nmarcovecchio/cof/docs/voice/operators/README.md

# Operadores

Una carpeta por red. Lo que acá se afirma salió de pruebas en lab, no de
la ficha comercial del operador.

| Carpeta | Red | MCC/MNC | Lab |
|---|---|---|---|
| [claro-ar.md](claro-ar.md) | Claro Argentina | `722310` | `cof-test`, A7672SA-FASE |

Cuando entre otra SIM, copiá el mismo esquema de eventos (`ATD`, ringing,
reject, no-answer, answer, hangup) y no reutilices las conclusiones de Claro.
