nmarcovecchio/cof/hardware/kicad/01-alimentacion.kicad_sch

## KiCad design hardware/kicad/01-alimentacion.kicad_sch (2026-10-06)

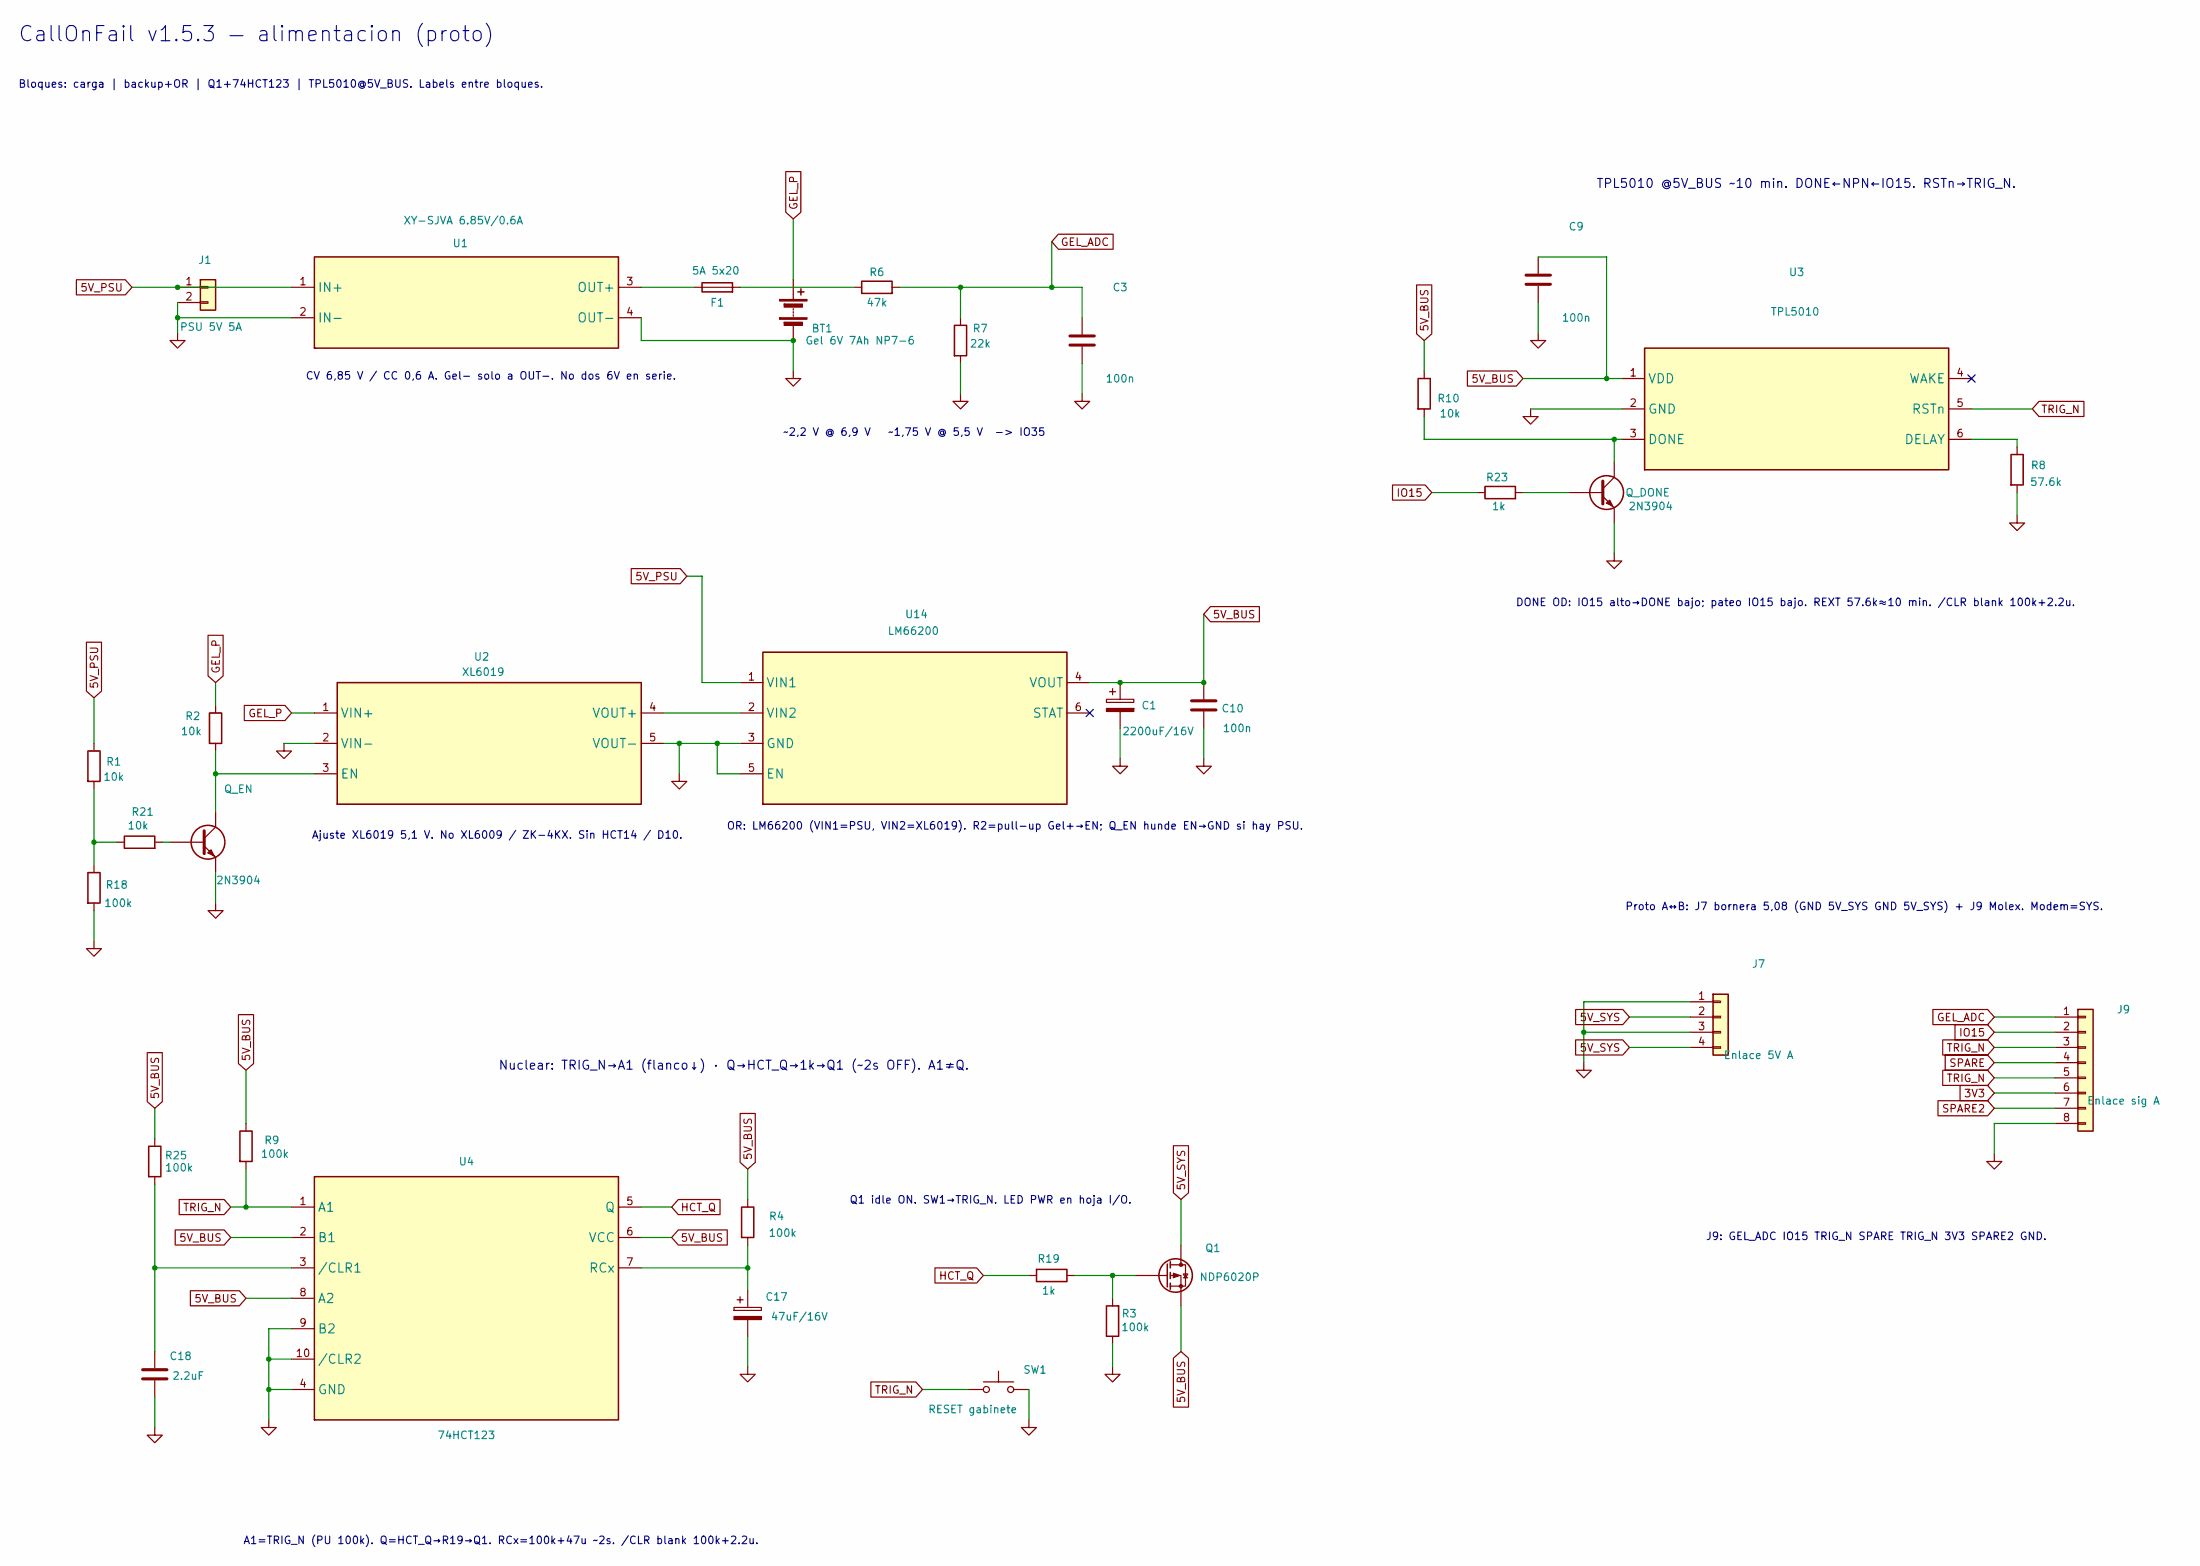
[picture p5: schematic 01-alimentacion.kicad_sch]

Parts:
BT1: Gel 6V 7Ah NP7-6
C1: 2200uF/16V
C3, C9, C10: 100n
C17: 47uF/16V
C18: 2.2uF
F1: 5A 5x20
J1: PSU 5V 5A
J7: Enlace 5V A
J9: Enlace sig A
Q1: NDP6020P
Q_DONE: 2N3904
Q_EN: 2N3904
R1, R2, R10, R21: 10k
R3, R4, R9, R18, R25: 100k
R6: 47k
R7: 22k
R8: 57.6k
R19, R23: 1k
SW1: RESET gabinete
U1: XY-SJVA 6.85V/0.6A
U2: XL6019
U3: TPL5010
U4: 74HCT123
U14: LM66200

Connections:
3V3: J9.6
5V_BUS: C1.1, C9.1, C10.1, Q1.S, R4.1, R9.1, R10.1, R25.1, U3.1 (VDD), U4.2 (B1), U4.6 (VCC), U4.8 (A2), U14.4 (VOUT)
5V_PSU: J1.1, R1.1, U1.1 (IN+), U14.1 (VIN1)
5V_SYS: J7.2, J7.4, Q1.D
GEL_ADC: C3.1, J9.1, R6.2, R7.1
GEL_P: BT1.1 (+), R2.1, U2.1 (VIN+)
GND: BT1.2 (-), C1.2, C3.2, C9.2, C10.2, C17.2, C18.2, J1.2, J7.1, J7.3, J9.8, Q_DONE.E, Q_EN.E, R3.1, R7.2, R8.2, R18.2, SW1.2, U1.2 (IN-), U1.4 (OUT-), U2.2 (VIN-), U2.5 (VOUT-), U3.2 (GND), U4.4 (GND), U4.9 (B2), U4.10 (/CLR2), U14.3 (GND), U14.5 (EN)
HCT_Q: R19.2, U4.5 (Q)
IO15: J9.2, R23.1
unnamed: C17.1, R4.2, U4.7 (RCx)
unnamed: C18.1, R25.2, U4.3 (/CLR1)
unnamed: F1.1, U1.3 (OUT+)
unnamed: F1.2, R6.1
unnamed: Q1.G, R3.2, R19.1
unnamed: Q_DONE.B, R23.2
unnamed: Q_DONE.C, R10.2, U3.3 (DONE)
unnamed: Q_EN.B, R21.2
unnamed: Q_EN.C, R2.2, U2.3 (EN)
unnamed: R1.2, R18.1, R21.1
unnamed: R8.1, U3.6 (DELAY)
unnamed: U2.4 (VOUT+), U14.2 (VIN2)
SPARE: J9.4
SPARE2: J9.7
TRIG_N: J9.3, J9.5, R9.2, SW1.1, U3.5 (RSTn), U4.1 (A1)

Notes on the sheet:
Q1 idle ON. SW1→TRIG_N. LED PWR en hoja I/O.
TPL5010 @5V_BUS ~10 min. DONE←NPN←IO15. RSTn→TRIG_N.
OR: LM66200 (VIN1=PSU, VIN2=XL6019). R2=pull-up Gel+→EN; Q_EN hunde EN→GND si hay PSU.
Ajuste XL6019 5,1 V. No XL6009 / ZK-4KX. Sin HCT14 / D10.
~2,2 V @ 6,9 V ~1,75 V @ 5,5 V -> IO35
Proto A↔B: J7 bornera 5,08 (GND 5V_SYS GND 5V_SYS) + J9 Molex. Modem=SYS.
J9: GEL_ADC IO15 TRIG_N SPARE TRIG_N 3V3 SPARE2 GND.
DONE OD: IO15 alto→DONE bajo; pateo IO15 bajo. REXT 57.6k≈10 min. /CLR blank 100k+2.2u.
Bloques: carga | backup+OR | Q1+74HCT123 | TPL5010@5V_BUS. Labels entre bloques.
A1=TRIG_N (PU 100k). Q=HCT_Q→R19→Q1. RCx=100k+47u ~2s. /CLR blank 100k+2.2u.
CallOnFail v1.5.3 — alimentacion (proto)
CV 6,85 V / CC 0,6 A. Gel- solo a OUT-. No dos 6V en serie.
Nuclear: TRIG_N→A1 (flanco↓) · Q→HCT_Q→1k→Q1 (~2s OFF). A1≠Q.
