nmarcovecchio/cof/hardware/kicad/02-io.kicad_sch

## KiCad design hardware/kicad/02-io.kicad_sch (2026-10-06)

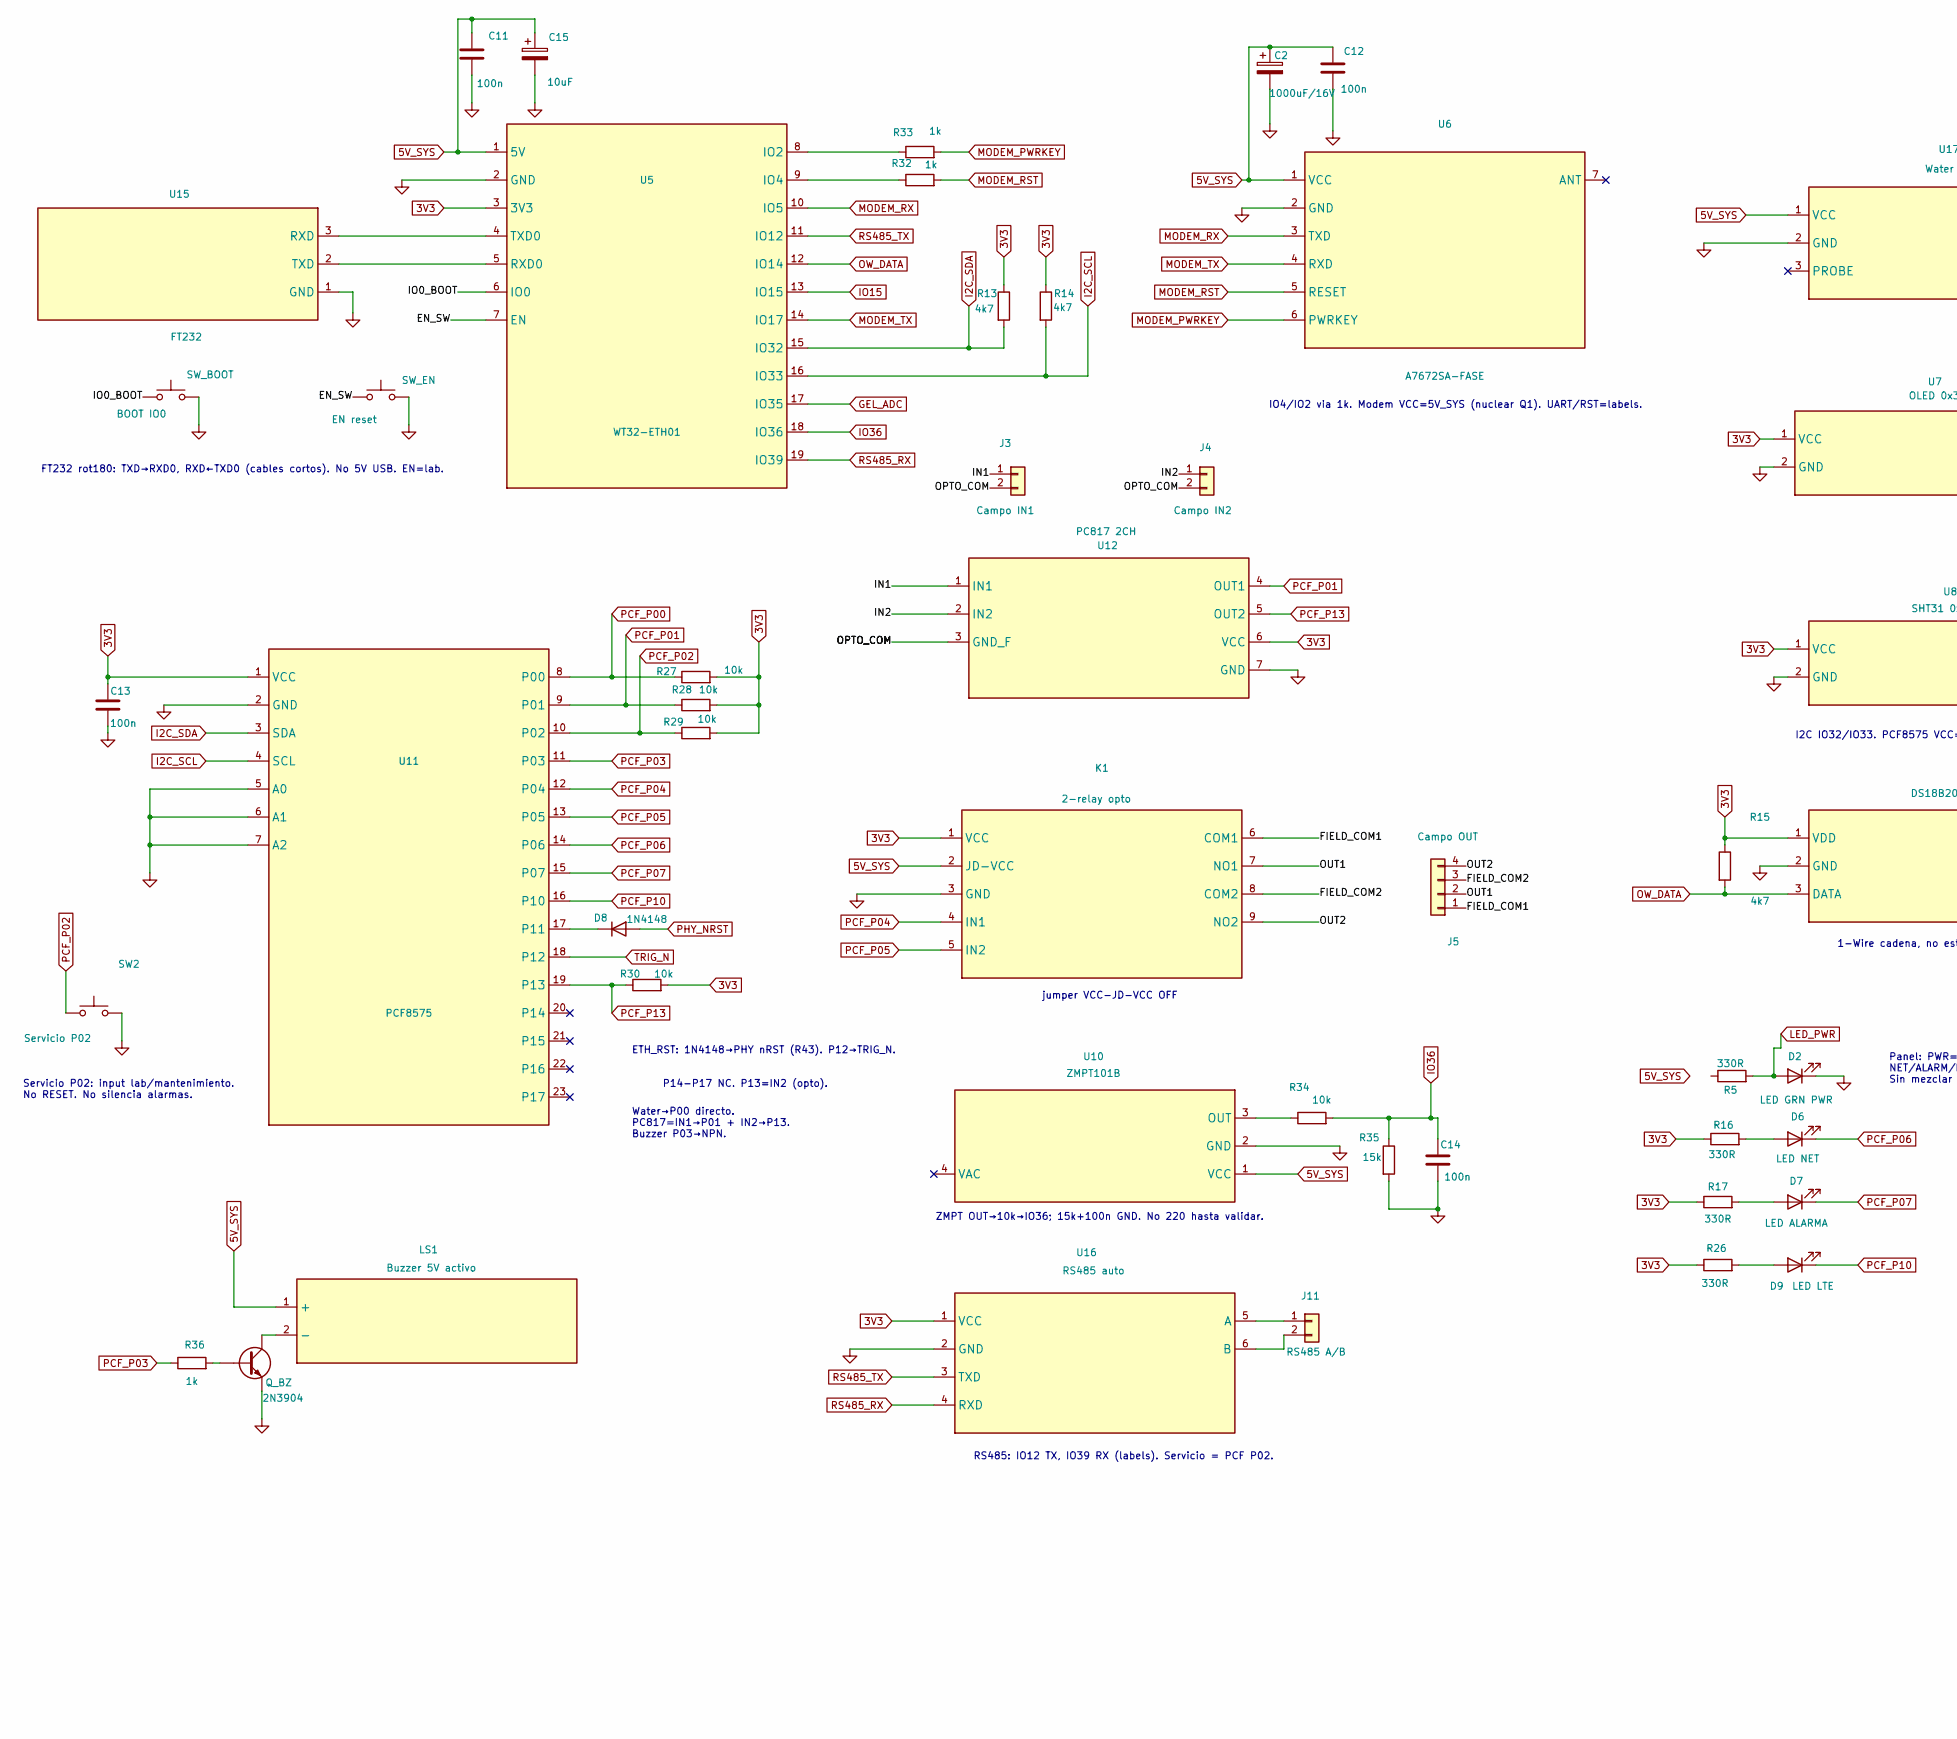
[picture p6: schematic 02-io.kicad_sch, part in row 1, column 1]

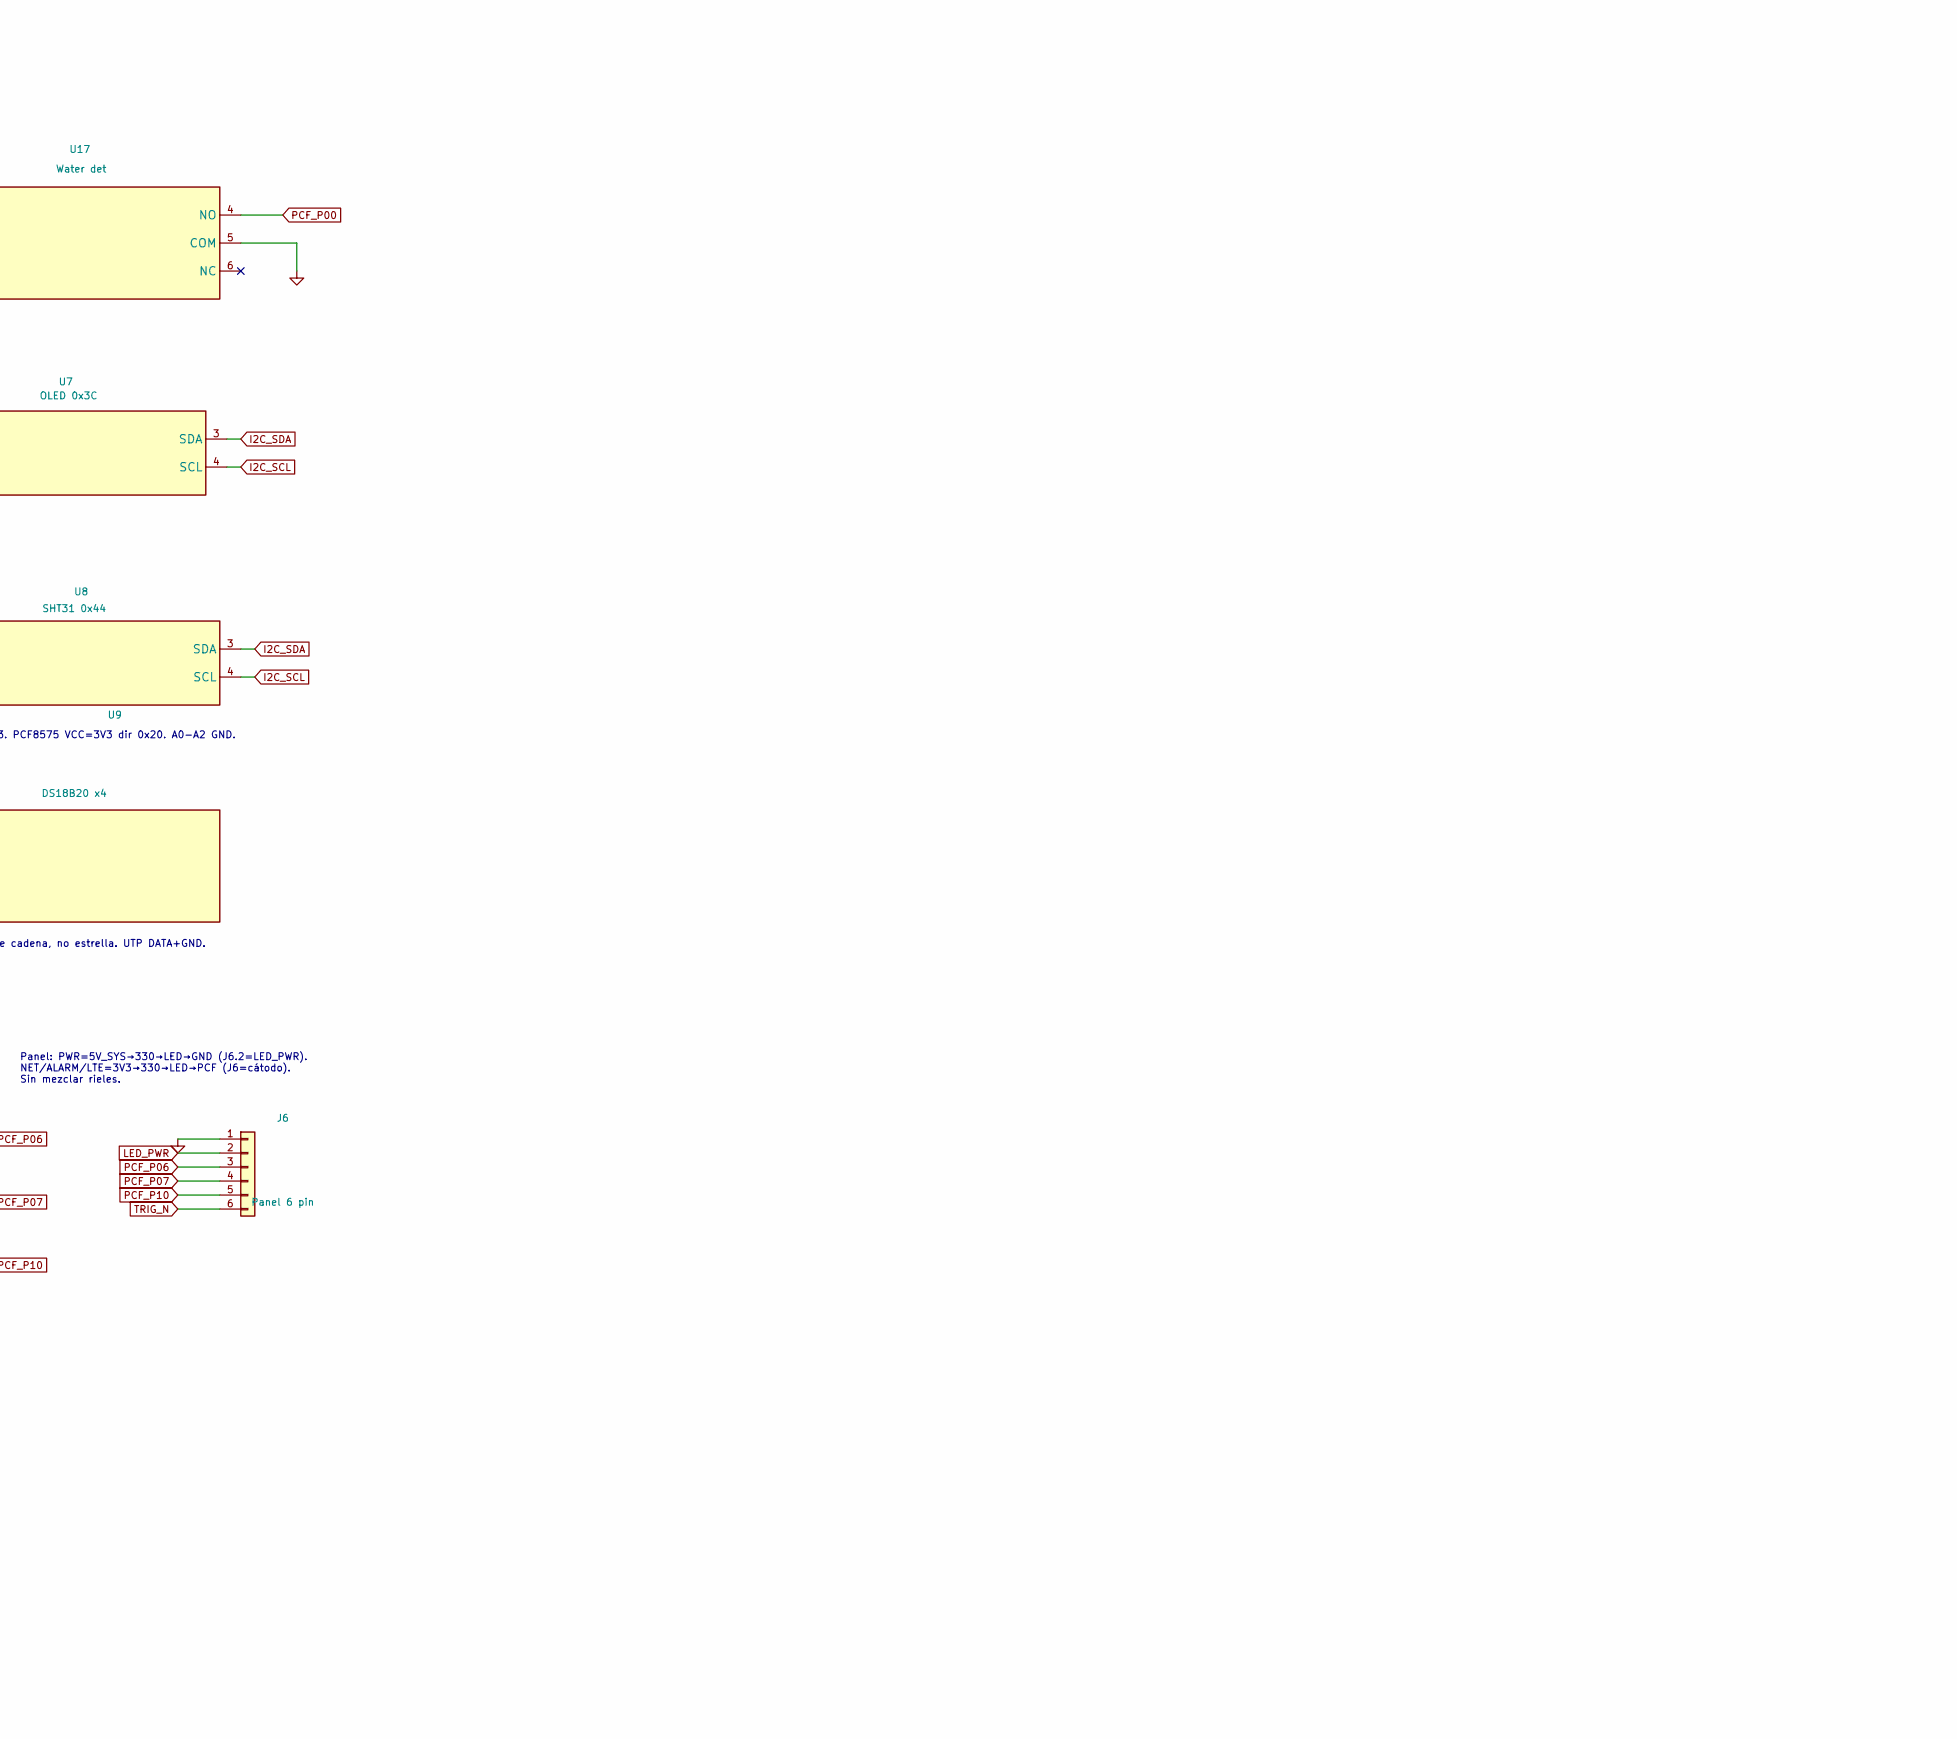
[picture p7: schematic 02-io.kicad_sch, part in row 1, column 2]

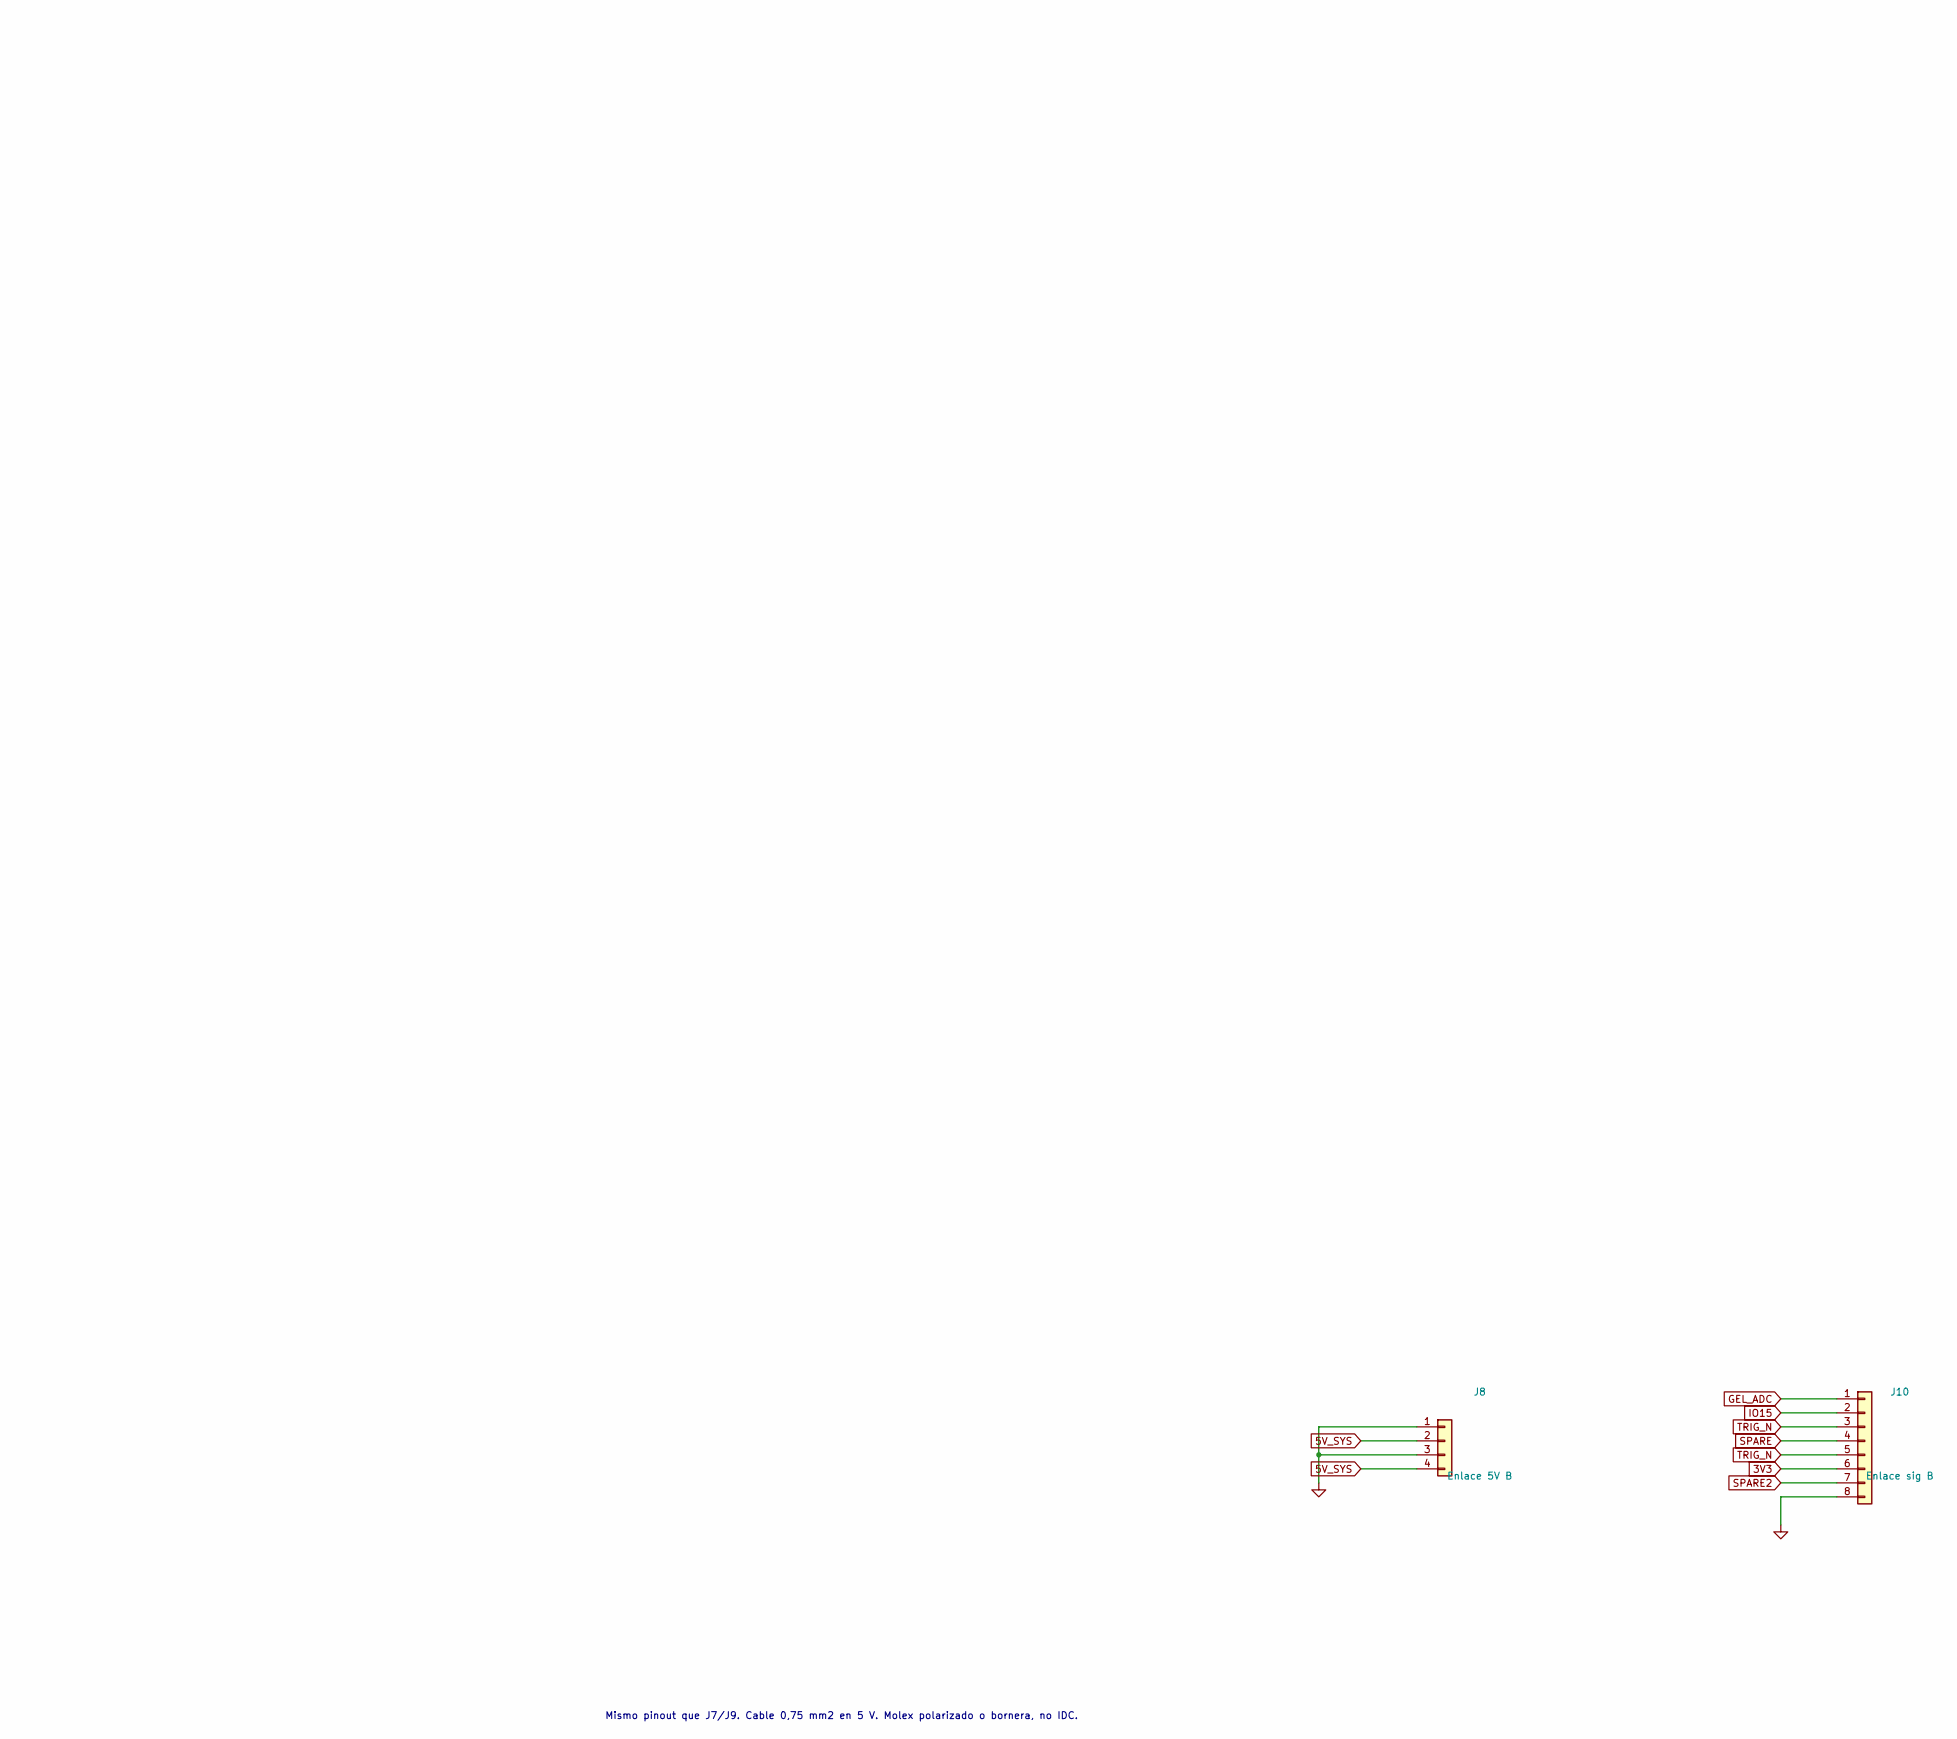
[picture p8: schematic 02-io.kicad_sch, part in row 2, column 2]

Parts:
C2: 1000uF/16V
C11, C12, C13, C14: 100n
C15: 10uF
D2: LED GRN PWR
D6: LED NET
D7: LED ALARMA
D8: 1N4148
D9: LED LTE
J3: Campo IN1
J4: Campo IN2
J5: Campo OUT
J6: Panel 6 pin
J8: Enlace 5V B
J10: Enlace sig B
J11: RS485 A/B
K1: 2-relay opto
LS1: Buzzer 5V activo
Q_BZ: 2N3904
R5, R16, R17, R26: 330R
R13, R14, R15: 4k7
R27, R28, R29, R30, R34: 10k
R32, R33, R36: 1k
R35: 15k
SW2: Servicio P02
SW_BOOT: BOOT IO0
SW_EN: EN reset
U5: WT32-ETH01
U6: A7672SA-FASE
U7: OLED 0x3C
U8: SHT31 0x44
U9: DS18B20 x4
U10: ZMPT101B
U11: PCF8575
U12: PC817 2CH
U15: FT232
U16: RS485 auto
U17: Water det

Connections:
3V3: C13.1, J10.6, K1.1 (VCC), R13.1, R14.1, R15.1, R16.1, R17.1, R26.1, R27.2, R28.2, R29.2, R30.2, U5.3 (3V3), U7.1 (VCC), U8.1 (VCC), U9.1 (VDD), U11.1 (VCC), U12.6 (VCC), U16.1 (VCC)
5V_SYS: C2.1, C11.1, C12.1, C15.1, J8.2, J8.4, K1.2 (JD-VCC), LS1.1 (+), U5.1 (5V), U6.1 (VCC), U10.1 (VCC), U17.1 (VCC)
EN_SW: SW_EN.1, U5.7 (EN)
FIELD_COM1: J5.1, K1.6 (COM1)
FIELD_COM2: J5.3, K1.8 (COM2)
GEL_ADC: J10.1, U5.17 (IO35)
GND: C2.2, C11.2, C12.2, C13.2, C14.2, C15.2, D2.1 (K), J6.1, J8.1, J8.3, J10.8, K1.3 (GND), Q_BZ.E, R35.2, SW2.2, SW_BOOT.2, SW_EN.2, U5.2 (GND), U6.2 (GND), U7.2 (GND), U8.2 (GND), U9.2 (GND), U10.2 (GND), U11.2 (GND), U11.5 (A0), U11.6 (A1), U11.7 (A2), U12.7 (GND), U15.1 (GND), U16.2 (GND), U17.2 (GND), U17.5 (COM)
I2C_SCL: R14.2, U5.16 (IO33), U7.4 (SCL), U8.4 (SCL), U11.4 (SCL)
I2C_SDA: R13.2, U5.15 (IO32), U7.3 (SDA), U8.3 (SDA), U11.3 (SDA)
IN1: J3.1, U12.1 (IN1)
IN2: J4.1, U12.2 (IN2)
IO0_BOOT: SW_BOOT.1, U5.6 (IO0)
IO15: J10.2, U5.13 (IO15)
IO36: C14.1, R34.2, R35.1, U5.18 (IO36)
LED_PWR: D2.2 (A), J6.2, R5.2
MODEM_PWRKEY: R33.2, U6.6 (PWRKEY)
MODEM_RST: R32.2, U6.5 (RESET)
MODEM_RX: U5.10 (IO5), U6.3 (TXD)
MODEM_TX: U5.14 (IO17), U6.4 (RXD)
unnamed: D6.2 (A), R16.2
unnamed: D7.2 (A), R17.2
unnamed: D8.1 (K), U11.17 (P11)
unnamed: D9.2 (A), R26.2
unnamed: J11.1, U16.5 (A)
unnamed: J11.2, U16.6 (B)
unnamed: LS1.2 (-), Q_BZ.C
unnamed: Q_BZ.B, R36.2
unnamed: R32.1, U5.9 (IO4)
unnamed: R33.1, U5.8 (IO2)
unnamed: R34.1, U10.3 (OUT)
unnamed: U5.5 (RXD0), U15.2 (TXD)
unnamed: U5.4 (TXD0), U15.3 (RXD)
OPTO_COM: J3.2, J4.2, U12.3 (GND_F)
OUT1: J5.2, K1.7 (NO1)
OUT2: J5.4, K1.9 (NO2)
OW_DATA: R15.2, U5.12 (IO14), U9.3 (DATA)
PCF_P00: R27.1, U11.8 (P00), U17.4 (NO)
PCF_P01: R28.1, U11.9 (P01), U12.4 (OUT1)
PCF_P02: R29.1, SW2.1, U11.10 (P02)
PCF_P03: R36.1, U11.11 (P03)
PCF_P04: K1.4 (IN1), U11.12 (P04)
PCF_P05: K1.5 (IN2), U11.13 (P05)
PCF_P06: D6.1 (K), J6.3, U11.14 (P06)
PCF_P07: D7.1 (K), J6.4, U11.15 (P07)
PCF_P10: D9.1 (K), J6.5, U11.16 (P10)
PCF_P13: R30.1, U11.19 (P13), U12.5 (OUT2)
PHY_NRST: D8.2 (A)
RS485_RX: U5.19 (IO39), U16.4 (RXD)
RS485_TX: U5.11 (IO12), U16.3 (TXD)
SPARE: J10.4
SPARE2: J10.7
TRIG_N: J6.6, J10.3, J10.5, U11.18 (P12)

Notes on the sheet:
Mismo pinout que J7/J9. Cable 0,75 mm2 en 5 V. Molex polarizado o bornera, no IDC.
I2C IO32/IO33. PCF8575 VCC=3V3 dir 0x20. A0-A2 GND.
ETH_RST: 1N4148→PHY nRST (R43). P12→TRIG_N.
Water→P00 directo. PC817=IN1→P01 + IN2→P13. Buzzer P03→NPN.
1-Wire cadena, no estrella. UTP DATA+GND.
Panel: PWR=5V_SYS→330→LED→GND (J6.2=LED_PWR). NET/ALARM/LTE=3V3→330→LED→PCF (J6=cátodo). Sin mezclar rieles.
RS485: IO12 TX, IO39 RX (labels). Servicio = PCF P02.
ZMPT OUT→10k→IO36; 15k+100n GND. No 220 hasta validar.
P14-P17 NC. P13=IN2 (opto).
IO4/IO2 via 1k. Modem VCC=5V_SYS (nuclear Q1). UART/RST=labels.
FT232 rot180: TXD→RXD0, RXD←TXD0 (cables cortos). No 5V USB. EN=lab.
GPIO: 0 BOOT 2 PWRKEY 4 RESET 5/17 modem 12/39 RS485 14 1-Wire 15 DONE 32/33 I2C 35 gel 36 ZMPT EN=lab P12=TRIG_N↓
Servicio P02: input lab/mantenimiento. No RESET. No silencia alarmas.
jumper VCC-JD-VCC OFF
