nmarcovecchio/cof/firmware/src/modem_at.cpp

#include "cof_config.h"
#include "cof_state.h"
#include <Arduino.h>
#include <Wire.h>
#include <esp_task_wdt.h>

// Extracted verbatim from main.cpp, which used to hold every function

// Restore radio service after the modem gets stuck in a NO SERVICE state.
//
// Observed on hardware (2026-09-21): +CPIN: READY and AT+CIMI OK, but
// +CSQ: 99,99 and +CPSI: NO SERVICE,Online, with AT+CNACT? replying ERROR.
// AT+CMEE=2 and AT+CGATT=1 do not recover it and nothing else in the firmware
// did either; the only known cure was a physical power cycle, unavailable on a
// remote site. Escalate from the cheapest reset to the closest software
// equivalent of that power cycle.
//
// NOT A FIX - a mitigation. A healthy module never reaches stage 5, so when that
// log line appears the modem needs attention (power, antenna, SIM seating).
bool resetModemRadio(uint8_t stage) {
  if (!state.modemReady || state.callInProgress || state.otaInProgress) {
    return false;
  }
  setStatus("Modem reset");
  switch (stage) {
    case 1:
      // Gentlest possible nudge: ask the modem to re-select the operator. No
      // CGATT=0 detach and no PDP teardown here - detaching on a transient
      // "NO SERVICE" read *caused* the next registration flap and re-triggered
      // this ladder in a loop (8x "recovery started" on 2026-09-25). The
      // baseband reselects on its own; COPS=0 only nudges it. The grace window
      // in pollModem() already held off until NO SERVICE persisted.
      Serial.println("[modem] recovery 1/5: operator reselect (COPS=0)");
      sendAT("AT+COPS=0", "OK", 20000);
      break;
    case 2:
      // Re-attach to the packet domain WITHOUT detaching first. CGATT=1 is
      // idempotent when already attached and costs nothing; a plain re-attach
      // fixes a stale attach state without the detach flap.
      Serial.println("[modem] recovery 2/5: PS re-attach + operator auto");
      sendAT("AT+CGATT=1", "OK", 15000);
      sendAT("AT+COPS=0", "OK", 20000);
      break;
    case 3:
      // Radio off/on. This is the first step that actually cycles the RF; the
      // two gentler steps above cover the common transient reselection case.
      Serial.println("[modem] recovery 3/5: radio cycle (CFUN=0/1)");
      stopLtePdp();
      sendAT("AT+CFUN=0", "OK", 10000);
      waitWithWatchdog(2000);
      sendAT("AT+CFUN=1", "OK", 15000);
      sendAT("AT+CEMODE=3", "OK", 3000);
      sendAT("AT+CEVDP=3", "OK", 3000);
      sendAT("AT+COPS=0", "OK", 30000);
      break;
    case 4:
      // Software reset of the whole module. Watch the CPIN state afterwards: a
      // module that comes back with +CPIN: NOT READY points at SIM seating or
      // power rather than firmware.
      Serial.println("[modem] recovery 4/5: modem reset (CFUN=1,1)");
      sendAT("AT+CFUN=1,1", "OK", 5000);
      waitWithWatchdog(15000);
      // CFUN=1,1 drops ATE0, CGDCONT, CGAUTH, CGSMS, CMGF, CSCA and the voice
      // settings, so re-apply them. Without this the module recovers RF but comes
      // back without the APN/SMS configuration and the PDP cannot come up.
      initModem();
      break;
    default:
      // Stage 5, or AT+CFUN=1,1 is still settling. Reboot so the radio comes up
      // from a cold power-on anyway. Stage 4 already reset the module, so its
      // configuration has to be re-applied on the way back up; initModem() in
      // setup() covers that.
      Serial.println("[modem] recovery 5/5: modem still dead, restarting ESP32");
      stopLtePdp();
      setStatus("Restart (modem)");
      delay(300);
      ESP.restart();
      return false;
  }
  return waitForRadioService(45000, false);
}
void beginInternalWatchdog() {
#if ESP_ARDUINO_VERSION_MAJOR >= 3
  esp_task_wdt_config_t config = {
    .timeout_ms = kWatchdogTimeoutSeconds * 1000,
    .idle_core_mask = (1 << portNUM_PROCESSORS) - 1,
    .trigger_panic = true,
  };
  esp_task_wdt_init(&config);
#else
  esp_task_wdt_init(kWatchdogTimeoutSeconds, true);
#endif
  esp_task_wdt_add(nullptr);
  Serial.printf("[wdt] internal watchdog enabled: %lu seconds\n", kWatchdogTimeoutSeconds);
}
void feedWatchdog() {
  esp_task_wdt_reset();
}
bool modemLineInteresting(const String& line) {
  String upper = line;
  upper.toUpperCase();
  return upper.indexOf("ATD") >= 0 || upper.indexOf("ATH") >= 0 ||
         upper.indexOf("CLCC") >= 0 || upper.indexOf("CEER") >= 0 ||
         upper.indexOf("BUSY") >= 0 || upper.indexOf("CARRIER") >= 0 ||
         upper.indexOf("VOICE") >= 0 || upper.indexOf("AUDIO") >= 0 ||
         upper.indexOf("COLP") >= 0 || upper.indexOf("CCMX") >= 0 ||
         upper.indexOf("NO ANSWER") >= 0 || upper.indexOf("CHUP") >= 0;
}
static void appendModemLogLine(String entry) {
  // Do not record the AT traffic of publishing uart-debug dumps themselves.
  if (uartDebugPublishing) {
    return;
  }
  entry.replace("\r", " ");
  entry.replace("\n", " | ");
  entry.trim();
  if (entry.length() == 0) {
    return;
  }
  const uint16_t lineMax = modemUartDebug ? kModemUartDebugLineMax : 140;
  if (entry.length() > lineMax) {
    entry = entry.substring(0, lineMax - 16) + "...(" + String(entry.length()) + "b)";
  }
  if (modemUartDebug) {
    entry = "T+" + String(millis()) + " " + entry;
  }
  // Debug ON: never drop lines from the live buffer — seal a chunk for later
  // MQTT publish, then keep appending. Debug OFF: old ring-tail behaviour.
  while (modemCallLog.length() + entry.length() + 1 > kModemCallLogMax) {
    if (modemUartDebug) {
      sealModemUartDebugChunk("overflow");
      if (modemCallLog.length() + entry.length() + 1 > kModemCallLogMax) {
        // Queue full and still no room: last resort drop oldest live line.
        const int cut = modemCallLog.indexOf('\n');
        if (cut < 0) {
          modemCallLog = "";
          break;
        }
        modemCallLog = modemCallLog.substring(cut + 1);
      }
    } else {
      const int cut = modemCallLog.indexOf('\n');
      if (cut < 0) {
        modemCallLog = "";
        break;
      }
      modemCallLog = modemCallLog.substring(cut + 1);
    }
  }
  if (modemCallLog.length() > 0) {
    modemCallLog += '\n';
  }
  modemCallLog += entry;
}
// The MQTT password and the APN password are the last quoted argument of
// AT+CMQTTCONNECT= and AT+CGAUTH=, and this log is published to the panel (and
// stored in the events table) whenever UART debug is ON. Two adjacent quoted
// arguments (`","`) is what tells those apart from the single-quoted-argument
// forms. The READ response of AT+CMQTTCONNECT? echoes the same credentials back
// as `+CMQTTCONNECT: <idx>,"tcp://…",…,"user","pass"` (colon, not `=`), so it
// must be redacted too; a CONNECT without credentials (or the `+CMQTTCONNECT:
// 0,0` result) has no `","` and stays intact.
static String redactTrailingCredential(const String& line) {
  if (line.indexOf("+CMQTTCONNECT=") < 0 && line.indexOf("+CMQTTCONNECT:") < 0 &&
      line.indexOf("+CGAUTH=") < 0) {
    return line;
  }
  const int pair = line.indexOf("\",\"");
  if (pair < 0) {
    return line;
  }
  return line.substring(0, pair + 2) + "<redacted>\"";
}
void appendModemLog(char direction, const String& text) {
  // Lab UART debug logs every AT line; call/LTE progress keep the old filter.
  if (!state.callInProgress && !reportTestCallProgress && !reportLteProgress && !modemUartDebug) {
    return;
  }
  // Both directions: a module that rebooted comes back with echo ON, so the
  // command (with its credentials) also arrives inside the response.
  String line = redactTrailingCredential(text);
  line.replace("\r", " ");
  line.replace("\n", " | ");
  line.trim();
  if (line.length() == 0) {
    return;
  }
  if (!modemUartDebug && !reportLteProgress && !modemLineInteresting(line)) {
    return;
  }
  appendModemLogLine(String(direction == '>' ? ">> " : "<< ") + line);
}
void appendModemLogForced(const String& text) {
  appendModemLogLine(text);
}
void waitWithWatchdog(uint32_t ms) {
  const uint32_t startedAt = millis();
  while (millis() - startedAt < ms) {
    feedWatchdog();
    if (state.mqttConnected) {
      mqttClient.loop();
    }
    delay(50);
  }
}
// The A7672 emits *ATREADY: 1 (and *ATREADY: 0) only when the module (re)boots.
// A spontaneous reset or the recovery ladder's CFUN=1,1 both produce it, and it
// is the only unambiguous sign the AT channel has been torn down: everything
// cached about the module - PDP, socket, SIM, radio config, ATE0 - is now stale.
//
// Called ONLY from pollModem(), never from the AT read path. readModemUntil() and
// noteUrc() just set `modemRebootUrcSeen = true` when they see *ATREADY; that
// flag is acted on here, outside of any in-flight command. The previous design
// called this from readModemUntil()/flushModemInput() (i.e. mid-command, often
// inside initModem() itself) and reset modemReady during the very init that was
// re-establishing it, wedging the device in "L no AT" + "Wait SIM" (2026-09-25).
void noteModemRebootDetected() {
  if (!state.modemReady && !state.simReady && !state.lteDataUp && !state.lteMqttTransport) {
    return;  // already flagged; avoid log spam
  }
  Serial.println("[modem] *ATREADY detected: modem rebooted, flagging for re-init");
  noteLteSessionDrop("atready");
  noteModemUnstable("atready");
  state.modemReady = false;
  state.simReady = false;
  state.networkRegistered = false;
  state.lteDataUp = false;
  state.lteMqttTransport = false;
  state.lteIpAddress = "-";
  lteMqttClient.sockOpen = false;
  lteMqttClient.atCommandBusy = false;
  lteMqttClient.drainRx();
}
// A modem that reboots (CFUN=1,1 or spontaneous) comes back with echo ON; ATE0
// is only sent from initModem() and a reboot does not re-run it. Detect the
// echoed command in a response and turn echo off again so the next commands
// parse cleanly. Never re-issues the caller's command: it already ran.
void ensureEchoOffIfNeeded(const String& command, const String& response) {
  if (command.length() == 0 || command == "ATE0") {
    return;
  }
  if (!response.startsWith(command)) {
    return;
  }
  Serial.println("[modem] echo detected, re-sending ATE0");
  ModemSerial.print("ATE0\r\n");
  String discard;
  readModemUntil(1000, "OK");
}
// String::indexOf() is strstr and stops at the first 0x00. The A7672 prefixes
// a spontaneous reboot with a NUL (`\0\r\n*ATREADY`), so the URC was invisible
// and 0.2.94 kept sending CMQTTDISC/REL/STOP through the boot (ethernet unplug,
// 2026-09-26 13:25).
bool textHasAtReady(const String& text) {
  static const char kTag[] = "*ATREADY";
  constexpr int kTagLen = 8;
  if (text.length() < kTagLen) {
    return false;
  }
  for (int i = 0; i <= text.length() - kTagLen; i++) {
    bool match = true;
    for (int j = 0; j < kTagLen; j++) {
      if (text[i + j] != kTag[j]) {
        match = false;
        break;
      }
    }
    if (match) {
      return true;
    }
  }
  return false;
}
void flushModemInput() {
  // Bound the drain: a module spewing (echo ON / boot-URC flood / line noise)
  // used to make this loop run forever and block every AT command that follows
  // (sendAT() calls it first). Cap the bytes per call; the next call drains more.
  int drained = 0;
  String swept;
  while (ModemSerial.available() && drained < 1024) {
    const char c = static_cast<char>(ModemSerial.read());
    drained++;
    if (state.callInProgress) {
      pendingCallUrcs += c;
    } else {
      pendingModemUrcs += c;
      swept += c;
      if (swept.length() > 400) {
        swept.remove(0, swept.length() - 200);
      }
      if (pendingModemUrcs.length() > 2048) {
        pendingModemUrcs.remove(0, pendingModemUrcs.length() - 1024);
      }
    }
  }
  // sendAT() drains the UART before every command. A +CMQTTSUB / +CMQTTRX that
  // arrived after the previous OK lives in that drain and never reaches
  // cmqttLoop(). Record it; the bytes still go to pendingModemUrcs as before.
  const int at = swept.indexOf("+CMQTT");
  if (at >= 0) {
    appendModemLogForced(swept.substring(at));
  }
  if (textHasAtReady(swept)) {
    modemRebootUrcSeen = true;
  }
}
String readModemUntil(uint32_t timeoutMs, const String& token, const String& errorToken) {
  String response;
  bool rebootSeen = false;
  const uint32_t startedAt = millis();
  while (millis() - startedAt < timeoutMs) {
    feedWatchdog();
    // Pump MQTT on every path. `if (!loop())` below means "PINGRESP missing or
    // socket dead", not "no data available" (loop() returns true when idle), so
    // the return value is the liveness signal we actually want.
    //
    // Except while `LteMqttClient::write()` owns the line: this same loop runs
    // inside its `AT+CIPSEND` prompt/ACK waits, and both things the pump can do
    // - `available()` issuing `AT+CIPRXGET` and `loop()` emitting a PINGREQ -
    // are writes to the module that corrupt the exchange. The send is waiting
    // on the prompt it just paid for; nothing may talk over it.
    //
    // Native CMQTT (COF_LTE_MQTT_NATIVE) is excluded for the same reason and one
    // more: the module keepalives by itself, and cmqttLoop() reads the same UART
    // this function is draining, so pumping it here would steal the AT response.
#if COF_LTE_MQTT_NATIVE
    if (state.mqttConnected && !state.lteMqttTransport && !lteMqttClient.atCommandBusy) {
#else
    if (state.mqttConnected && !lteMqttClient.atCommandBusy) {
#endif
      if (mqttClient.loop()) {
        lastMqttOkMs = millis();
      } else {
        state.mqttConnected = false;
      }
    }
    // Drain a bounded chunk per pass and re-check the deadline inside the drain.
    // A module that keeps spewing (echo ON, boot-URC flood, noise) used to make
    // this inner loop run forever - never re-checking the timeout, never feeding
    // the watchdog - and grow `response` without limit until the heap ran out.
    // That is the "UART hangs everything" failure (see BACKLOG §6h / 0.2.77).
    for (int drained = 0; drained < 256 && millis() - startedAt < timeoutMs; drained++) {
      if (!ModemSerial.available()) {
        break;
      }
      const char c = static_cast<char>(ModemSerial.read());
      response += c;
      // A module reboot emits *ATREADY as a URC, possibly in the middle of the
      // command we are waiting on. Detect it cheaply at line boundaries.
      if (!rebootSeen && (c == '\n' || c == '\r') && textHasAtReady(response)) {
        rebootSeen = true;
        // The module just rebooted under this command. Waiting out the rest of
        // the timeout (and the CMQTT commands that follow) is what kept talking
        // to a modem that was still emitting SMS DONE / PB DONE (2026-09-26,
        // clear_wifi -> *ATREADY inside CMQTTCONNECT, then NO SERVICE).
        modemRebootUrcSeen = true;
        return response;
      }
      // Optional early-exit token: stop draining the moment an error marker
      // appears, instead of burning the whole timeout waiting for a success
      // token that will never arrive (e.g. +CMGS answered with +CMS ERROR, no
      // "OK"). Checked per char like the success token so a slow error does not
      // pin us to the full timeout.
      if (errorToken.length() > 0 && response.indexOf(errorToken) >= 0) {
        if (rebootSeen) {
          modemRebootUrcSeen = true;
        }
        return response;
      }
      if (token.length() == 0) {
        continue;
      }
      const int tagAt = response.indexOf(token);
      if (tagAt < 0) {
        continue;
      }
      if (!token.endsWith(":")) {
        if (rebootSeen) {
          modemRebootUrcSeen = true;
        }
        return response;
      }
      for (int i = tagAt + token.length(); i < response.length(); i++) {
        if (response[i] == '\n' || response[i] == '\r') {
          if (rebootSeen) {
            modemRebootUrcSeen = true;
          }
          return response;
        }
      }
    }
    // Keep only the tail: what we search for (the token) always arrives last, and
    // an unbounded buffer is exactly the OOM the drain cap is meant to prevent.
    if (response.length() > 4096) {
      response = response.substring(response.length() - 4096);
    }
    delay(10);
  }
  if (rebootSeen) {
    modemRebootUrcSeen = true;
  }
  return response;
}
bool sendAT(const String& command, const String& expected, uint32_t timeoutMs, String* responseOut) {
  flushModemInput();
  if (modemRebootUrcSeen && command.startsWith("AT+CMQTT")) {
    Serial.println("[modem] skip " + command + " (module rebooted, waiting for re-init)");
    appendModemLogForced("skip " + command + " (ATREADY)");
    if (responseOut != nullptr) {
      *responseOut = "";
    }
    return false;
  }
  Serial.println("[modem] >> " + command);
  appendModemLog('>', command);
  ModemSerial.print(command);
  ModemSerial.print("\r\n");
  String response = readModemUntil(timeoutMs, expected);
  response.trim();
  Serial.println("[modem] << " + response);
  appendModemLog('<', response);

  // A rebooted module echoes the command back; turn echo off for the commands
  // that follow. The command itself already ran, so do not re-issue it.
  ensureEchoOffIfNeeded(command, response);

  if (responseOut != nullptr) {
    *responseOut = response;
  }
  return expected.length() == 0 || response.indexOf(expected) >= 0;
}
bool modemWaitForPrompt(uint32_t timeoutMs) {
  const String response = readModemUntil(timeoutMs, ">");
  Serial.println("[modem] << " + response);
  return response.indexOf(">") >= 0;
}
bool csAttached() {
  return networkStatRegistered(state.cregStat);
}
void noteSubscriberIdentity() {
  String identity = state.imsi;
  if (state.operatorName.length() > 0) {
    if (identity.length() > 0) {
      identity += "|";
    }
    identity += state.operatorName;
  }
  if (identity.length() < 3) {
    return;
  }
  if (state.voiceIdentity == identity) {
    return;
  }
  if (state.voiceIdentity.length() > 0) {
    Serial.println("[modem] SIM/operator changed, relearning voice path");
    persistSkipGsm(false);
    persistObservedVoicePath("");
  }
  state.voiceIdentity = identity;
  preferences.putString("voiceId", identity);
}
void applyAdaptiveCemode();
void refreshCellularStatus() {
  String response;
  if (sendAT("AT+CREG?", "OK", 2000, &response)) {
    state.cregStat = parseCommaStat(response, "+CREG:");
  }
  if (sendAT("AT+CEREG?", "OK", 2000, &response)) {
    state.ceregStat = parseCommaStat(response, "+CEREG:");
  }
  if (sendAT("AT+CGREG?", "OK", 2000, &response)) {
    state.cgregStat = parseCommaStat(response, "+CGREG:");
  }
  if (sendAT("AT+COPS?", "OK", 3000, &response)) {
    const String name = extractQuoted(response);
    if (name.length() > 0) {
      state.operatorName = name;
    }
  }
  if (sendAT("AT+CSCA?", "OK", 3000, &response)) {
    const String smsc = extractQuoted(response);
    if (smsc.length() > 0) {
      state.smsc = smsc;
    }
  }
  if (sendAT("AT+CSQ", "OK", 2000, &response)) {
    const int marker = response.indexOf("+CSQ:");
    if (marker >= 0) {
      state.signalQuality = response.substring(marker + 5).toInt();
    }
  }
  if (state.modemModel.length() == 0 && sendAT("AT+CGMM", "OK", 2000, &response)) {
    const String model = firstNonEmptyAtLine(response);
    if (model.length() > 0) {
      state.modemModel = model;
    }
  }
  if (sendAT("AT+CPSI?", "OK", 3000, &response)) {
    String cpsi = extractAtTagValue(response, "+CPSI:");
    if (cpsi.length() > 96) {
      cpsi = cpsi.substring(0, 96);
    }
    if (cpsi.length() > 0) {
      state.radioInfo = cpsi;
      const int comma = cpsi.indexOf(',');
      state.radioMode = comma >= 0 ? cpsi.substring(0, comma) : cpsi;
      state.radioMode.trim();
    }
  }
  if (sendAT("AT+CNMP?", "OK", 2000, &response)) {
    state.cnmp = extractAtTagValue(response, "+CNMP:").toInt();
  }
  if (sendAT("AT+CAVIMS?", "OK", 2000, &response)) {
    state.imsVoice = extractAtTagValue(response, "+CAVIMS:").toInt();
  }
  if (sendAT("AT+CIREG?", "OK", 2000, &response)) {
    // +CIREG: <n>,<reg_info>[,<ext_info>]  (3GPP TS 27.007 §8.71).
    // reg_info (2nd field) is the IMS registration flag: 1 = registered.
    // ext_info (hex IMS capabilities) only appears when registered, so the
    // old lastIndexOf(',') read ext_info (e.g. "15") instead of reg_info and
    // imsVoiceReady() never saw the registration (2026-09-30, VoLTE enabled).
    const String value = extractAtTagValue(response, "+CIREG:");
    if (value.length() > 0) {
      String reg = value;
      const int firstComma = value.indexOf(',');
      if (firstComma >= 0) {
        reg = value.substring(firstComma + 1);
      }
      const int secondComma = reg.indexOf(',');
      if (secondComma >= 0) {
        reg = reg.substring(0, secondComma);
      }
      reg.trim();
      state.imsReg = reg.toInt();
    }
  }
  if (sendAT("AT+CIMI", "OK", 2000, &response)) {
    const String imsi = firstNonEmptyAtLine(response);
    if (imsi.length() >= 5) {
      state.imsi = imsi;
    }
  }

  state.networkRegistered = networkStatRegistered(state.cregStat) ||
                            networkStatRegistered(state.ceregStat) ||
                            networkStatRegistered(state.cgregStat);
  noteSubscriberIdentity();
  state.predictedVoicePath = inferVoicePath();

  Serial.printf("[modem] net registered=%s radio=%s voice=%s ims=%d creg=%d cereg=%d op=%s\n",
                state.networkRegistered ? "yes" : "no",
                state.radioMode.c_str(),
                state.predictedVoicePath.c_str(),
                state.imsReg,
                state.cregStat,
                state.ceregStat,
                state.operatorName.c_str());
  applyAdaptiveCemode();
}

// CEMODE has to follow the site, not a fixed choice: an IMS-registered site wants
// EPS-only (CEMODE=3) so voice/SMS ride VoLTE/SMSoIP, while a legacy site (2G or
// LTE with CSFB but no IMS) must keep the combined attach (CEMODE=1) or it loses
// CS SMS/SGs and CSFB voice entirely. Called from refreshCellularStatus() once
// +CIREG has answered, and from restorePacketServices() after a voice/SMS cycle.
int lastAppliedCemode = -1;
// While SMS is forcing the combined attach (CEMODE=1), suppress the adaptive
// switch so refreshCellularStatus() (invoked inside the attach wait loop) does
// not flip the mode back to 3 and kill the SGs path mid-submit.
static bool gSmsCsTransportActive = false;

void applyAdaptiveCemode() {
  if (gSmsCsTransportActive) {
    return;
  }
  const int wanted = imsVoiceReady() ? 3 : 1;
  if (wanted == lastAppliedCemode) {
    return;
  }
  String resp;
  if (sendAT("AT+CEMODE?", "OK", 2000, &resp)) {
    const int current = extractAtTagValue(resp, "+CEMODE:").toInt();
    if (current == wanted) {
      lastAppliedCemode = wanted;
      return;
    }
  }
  if (sendAT(String("AT+CEMODE=") + wanted, "OK", 3000)) {
    lastAppliedCemode = wanted;
    Serial.printf("[modem] CEMODE=%d (%s)\n", wanted,
                  wanted == 3 ? "IMS/VoLTE" : "CS/PS (2G/CSFB)");
  }
}

// MO SMS does not ride IMS on this operator (the A7672 sends AT+CMGS and the
// submit times out with +CMS ERROR: Network timeout even with +CIREG registered
// and the IMS bearer up on CID 8). The working path is CS/SGs, which needs the
// combined attach (CEMODE=1). Voice, in contrast, stays on VoLTE (CEMODE=3), so
// the two transports are exclusive and are switched per operation.
void enableCsSmsTransport() {
  gSmsCsTransportActive = true;
  setStatus("SMS CS attach");
  sendAT("AT+CEMODE=1", "OK", 3000);
  sendAT("AT+CEVDP=1", "OK", 3000);
  // Combined attach: wait until CREG reports registered (the CS/SGs side is up).
  const uint32_t startedAt = millis();
  while (millis() - startedAt < 30000) {
    feedWatchdog();
    if (state.mqttConnected) {
      mqttClient.loop();
    }
    refreshCellularStatus();
    if (csAttached()) {
      return;
    }
    waitWithWatchdog(2000);
  }
}

// Force IMS down so a retry MO SMS routes over CS/SGs instead of SMSoIP. On a
// VoLTE site whose data PDP (CID 1) is active (native MQTT), CEMODE=1 + CEVDP=1
// alone does NOT deregister IMS: the module keeps +CIREG: 2,1,15 and the CMGS
// keeps riding the unprovisioned SMSoIP path (+CMS ERROR: unknown error).
// Deactivating the IMS bearer (CID 8, auto-created by the module) and reporting
// "IMS voice not available" (CAVIMS=0) is what drops it. Best-effort: each
// command is ignored if unsupported; restoreImsMode() re-arms VoLTE afterwards.
static bool gImsDroppedForSms = false;
bool dropImsForSms() {
  gImsDroppedForSms = true;
  setStatus("SMS drop IMS");
  sendAT("AT+CGACT=0,8", "OK", 5000);
  sendAT("AT+CAVIMS=0", "OK", 3000);
  // Wait until +CIREG reports deregistered so the following CMGS cannot still
  // ride SMSoIP. ~15 s is enough for the IMS bearer teardown on A7672/Claro.
  const uint32_t startedAt = millis();
  while (millis() - startedAt < 15000) {
    feedWatchdog();
    if (state.mqttConnected) {
      mqttClient.loop();
    }
    refreshCellularStatus();
    if (!imsVoiceReady()) {
      return true;
    }
    waitWithWatchdog(1000);
  }
  refreshCellularStatus();
  return !imsVoiceReady();
}

// Return the modem to the idle mode for this site after an SMS: IMS (CEMODE=3,
// VoLTE) when registered, combined attach (CEMODE=1) on a legacy 2G/CSFB site.
void restoreImsMode() {
  gSmsCsTransportActive = false;
  lastAppliedCemode = -1;
  if (gImsDroppedForSms) {
    // dropImsForSms() took IMS down for the CS/SGs SMS; bring VoLTE back
    // explicitly. imsVoiceReady() is still false right now, so the adaptive
    // branch below would otherwise leave the site stuck CS-only.
    gImsDroppedForSms = false;
    sendAT("AT+CAVIMS=1", "OK", 3000);
    sendAT("AT+CEVDP=3", "OK", 3000);
    sendAT("AT+CIREG=2", "OK", 3000);
    sendAT("AT+CEMODE=3", "OK", 3000);
    lastAppliedCemode = 3;
    return;
  }
  if (imsVoiceReady()) {
    sendAT("AT+CEVDP=3", "OK", 3000);
    sendAT("AT+CAVIMS=1", "OK", 3000);
  }
  applyAdaptiveCemode();
}

void configureCellularApn() {
  state.apn = COF_MODEM_APN;
  // A modem reset mid-SMS clears any stale CS-transport override so the adaptive
  // mode logic can settle the site again on the way back up.
  gSmsCsTransportActive = false;
  gImsDroppedForSms = false;
  // Reset any forced band/mode. A reboot of the ESP32 or the modem during a stale
  // GSM-only lock (CNMP=13) used to leave the radio stuck at +CPSI: NO SERVICE on
  // a site with no 2G (2026-09-29, cof-test), because restoreAutoRadio()'s in-RAM
  // flag was gone. initModem() has no latch that forces this, so make it part of
  // the APN/mode configuration.
  sendAT("AT+CNMP=2", "OK", 10000);
  state.forcedGsmForCall = false;
  sendAT("AT+COPS=0", "OK", 5000);
  sendAT(String("AT+CGDCONT=1,\"IP\",\"") + COF_MODEM_APN + "\"", "OK", 3000);
  sendAT(String("AT+CGAUTH=1,1,\"") + COF_MODEM_APN_USER + "\",\"" + COF_MODEM_APN_PASS + "\"", "OK", 3000);
  sendAT("AT+CGATT=1", "OK", 15000);
  // CSMS=1 = Phase 2+ (GSM 07.05 phase 2+), which is required for SMS over
  // GPRS/PS. The module defaults to Phase 2 (CS-only SMS), so CGSMS=2 below has
  // no effect unless CSMS=1 is set first (A76XX AT manual §9.2.1).
  sendAT("AT+CSMS=1", "OK", 3000);
  // CGSMS=2 = "GPRS preferred" (SMS over PS/NAS on LTE, fall back to CS only
  // if PS is unavailable). CGSMS=1 is "circuit switched" (internally mapped to
  // 3 = CS preferred) and was forcing a 2G CS attempt per SMS, which on an
  // LTE-only site fails with +CMS ERROR and deactivates the data PDN
  // (+CGEV: ME PDN DEACT 1). A76XX AT manual §9.2.10.
  sendAT("AT+CGSMS=2", "OK", 3000);
  sendAT("AT+CSMP=17,167,0,0", "OK", 3000);
  sendAT("AT+CMGF=1", "OK", 3000);
  sendAT("AT+CNMI=2,1,0,0,0", "OK", 3000);
  // CEMODE=3 = "PS mode 1 of operation" (3GPP TS 27.007 §10.1.28): EPS-only,
  // voice-centric. Voice AND SMS go over IMS (VoLTE/SMSoIP); there is no CS
  // attach, so no CSFB and no SMS-over-SGs. CEMODE=1 was "CS/PS mode 1"
  // (combined attach = CSFB + SGs enabled) and made every MO SMS do CSFB: the
  // module dropped the data PDN (+CGEV: ME PDN DEACT 1) to reach 2G, which is
  // gone on this site, so the submit failed with +CMS ERROR (2026-09-30).
  //
  // Boot applies 3 provisionally; applyAdaptiveCemode() (called from
  // refreshCellularStatus(), where +CIREG is known) downgrades to 1 on any site
  // without IMS so the legacy 2G/CS path (and CSFB voice) keeps working.
  sendAT("AT+CEMODE=3", "OK", 3000);
  sendAT("AT+CEVDP=3", "OK", 3000);
  sendAT("AT+CAVIMS=1", "OK", 3000);
  sendAT("AT+CIREG=2", "OK", 2000);
  sendAT("AT+CGDCONT=2,\"IPV4V6\",\"ims\"", "OK", 3000);
  sendAT("AT+CRC=1", "OK", 2000);
  sendAT("AT+CVHU=0", "OK", 2000);

  String smscResponse;
  if (sendAT("AT+CSCA?", "OK", 3000, &smscResponse)) {
    state.smsc = extractQuoted(smscResponse);
  }
  if (state.smsc.length() < 8) {
    sendAT(String("AT+CSCA=\"") + COF_MODEM_SMSC + "\"", "OK", 3000);
    state.smsc = COF_MODEM_SMSC;
  }

  setStatus("Wait network");
  for (int attempt = 0; attempt < 8; attempt++) {
    feedWatchdog();
    refreshCellularStatus();
    if (state.networkRegistered) {
      setStatus("Network OK");
      return;
    }
    delay(2000);
  }
  setStatus("Network wait");
}
bool cpinResponseReady(const String& response) {
  const int idx = response.indexOf("+CPIN:");
  if (idx < 0) {
    return false;
  }
  return response.indexOf("NOT READY", idx) < 0 && response.indexOf("READY", idx) >= 0;
}
bool refreshSimReady() {
  if (!state.modemReady) {
    return false;
  }
  String response;
  if (!sendAT("AT+CPIN?", "OK", 3000, &response)) {
    return state.simReady;
  }
  if (!cpinResponseReady(response)) {
    return false;
  }
  if (!state.simReady) {
    state.simReady = true;
    configureCellularApn();
  }
  return true;
}
bool initModem() {
  ModemSerial.begin(115200, SERIAL_8N1, COF_PIN_MODEM_RX, COF_PIN_MODEM_TX);
  delay(300);

  bool gotAt = false;
  for (int attempt = 0; attempt < 5; attempt++) {
    if (sendAT("AT", "OK", 1000)) {
      gotAt = true;
      break;
    }
    delay(500);
  }

  if (!gotAt) {
    state.modemReady = false;
    state.simReady = false;
    setStatus("Modem no AT");
    return false;
  }

  state.modemReady = true;
  sendAT("ATE0", "OK", 1000);
  sendAT("ATI", "OK", 2000);

  String response;
  if (sendAT("AT+CGMM", "OK", 2000, &response)) {
    state.modemModel = firstNonEmptyAtLine(response);
  }

  state.simReady = false;
  for (int attempt = 0; attempt < 12; attempt++) {
    feedWatchdog();
    if (sendAT("AT+CPIN?", "OK", 2000, &response) && cpinResponseReady(response)) {
      state.simReady = true;
      break;
    }
    waitWithWatchdog(500);
  }

  state.modemAudioPlaybackSupported = sendAT("AT+CCMXPLAY=?", "OK", 3000);
  state.modemFileTransferSupported = sendAT("AT+CFTRANRX=?", "OK", 3000);

  if (state.simReady) {
    configureCellularApn();
  } else {
    setStatus("Wait SIM");
  }
  // initModem() IS the re-init that *ATREADY demands: it re-applies ATE0, APN,
  // SMS/voice settings and re-reads CPIN. Consume any *ATREADY seen during this
  // boot so pollModem() does not re-run the reset on a stale flag (§6h, 0.2.76).
  modemRebootUrcSeen = false;
  return true;
}
void refreshRadioMode() {
  String response;
  if (!sendAT("AT+CPSI?", "OK", 2000, &response)) {
    return;
  }
  String cpsi = extractAtTagValue(response, "+CPSI:");
  if (cpsi.length() > 96) {
    cpsi = cpsi.substring(0, 96);
  }
  if (cpsi.length() == 0) {
    return;
  }
  state.radioInfo = cpsi;
  const int comma = cpsi.indexOf(',');
  state.radioMode = comma >= 0 ? cpsi.substring(0, comma) : cpsi;
  state.radioMode.trim();
}
bool radioIsGsm() {
  return state.radioMode.indexOf("GSM") >= 0;
}
bool radioHasService() {
  return state.radioMode.length() > 0 &&
         state.radioMode.indexOf("NO SERVICE") < 0 &&
         state.radioMode.indexOf("No Service") < 0 &&
         state.networkRegistered;
}
// Does the radio report a usable RF state? False for the stuck state where CSQ is
// 99 and CPSI says NO SERVICE. networkRegistered ORs CREG/CEREG/CGREG, and CEREG
// keeps reporting "registered" on a stale context long after the radio lost
// service, so registration alone must not be trusted: CPSI's NO SERVICE is
// authoritative and is checked first.
bool radioReportsService() {
  if (state.radioMode.length() > 0 &&
      (state.radioMode.indexOf("NO SERVICE") >= 0 ||
       state.radioMode.indexOf("No Service") >= 0)) {
    return false;
  }
  if (state.networkRegistered) {
    return true;
  }
  return state.radioMode.length() > 0;
}
bool waitForRadioService(uint32_t timeoutMs, bool gsmOnly) {
  const uint32_t startedAt = millis();
  while (millis() - startedAt < timeoutMs) {
    feedWatchdog();
    if (state.mqttConnected) {
      mqttClient.loop();
    }
    refreshCellularStatus();
    if (radioHasService() && (!gsmOnly || radioIsGsm())) {
      return true;
    }
    waitWithWatchdog(2000);
  }
  if (gsmOnly && !(radioHasService() && radioIsGsm())) {
    // Surface what the radio actually looks like after a failed GSM-only wait.
    // Without this the call over LTE just went silent (2026-09-29) because the
    // CNMP=13 lock found no 2G and nothing in the trace said why.
    appendModemLogForced("GSM lock wait expired: radio=" + state.radioMode +
                         " csq=" + String(state.signalQuality));
  }
  return radioHasService() && (!gsmOnly || radioIsGsm());
}
int queryCpas() {
  String response;
  if (!sendAT("AT+CPAS", "OK", 3000, &response)) {
    return -1;
  }
  return extractAtTagValue(response, "+CPAS:").toInt();
}
bool radioIsOnline() {
  return state.radioInfo.indexOf("Online") >= 0 ||
         state.radioInfo.indexOf("ONLINE") >= 0;
}
bool waitUntilModemReady(bool forCall, uint32_t timeoutMs) {
  setStatus(forCall ? "Wait call ready" : "Wait SMS ready");
  const uint32_t startedAt = millis();
  while (millis() - startedAt < timeoutMs) {
    feedWatchdog();
    if (state.mqttConnected) {
      mqttClient.loop();
    }
    if (forCall ? isCallReady() : isSmsReady()) {
      waitWithWatchdog(1500);
      return true;
    }
    waitWithWatchdog(1500);
  }
  return forCall ? isCallReady() : isSmsReady();
}
void restoreAutoRadio() {
  // The flag is in RAM and is lost across a modem reboot, so it cannot be the only
  // trigger: after a reset during a stale GSM-only lock the module would stay
  // CNMP=13 on a site with no 2G and come up on NO SERVICE (2026-09-29). Ask the
  // module what mode it is actually in and clear a stale GSM-only lock regardless.
  if (!state.forcedGsmForCall && state.cnmp >= 0 && state.cnmp != 13) {
    return;
  }
  state.forcedGsmForCall = false;
  sendAT("AT+CNMP=2", "OK", 10000);
  state.cnmp = 2;
  waitForRadioService(20000, false);
}
// Pumps MQTT while waiting out a modem operation so a long AT exchange does not
// drop the broker connection. On LTE the MQTT keepalive is only 10 s while SMS
// commands can take up to 70 s, so without this the connection dies and the
// result event has nowhere to go.
void waitWithMqtt(uint32_t ms) {
  const uint32_t startedAt = millis();
  while (millis() - startedAt < ms) {
    feedWatchdog();
    if (!state.callInProgress && !state.otaInProgress && !state.audioSyncInProgress) {
      if (mqttClient.connected()) {
        state.mqttConnected = true;
        // loop() returns false only when the socket died or a PINGRESP never
        // arrived; a true return also means the keepalive was serviced.
        if (mqttClient.loop()) {
          lastMqttOkMs = millis();
        } else {
          state.mqttConnected = false;
        }
      }
    }
    delay(10);
  }
}
