nmarcovecchio/cof/firmware/src/cof_api.h

#pragma once
// Prototypes of every free function, grouped by the module that owns it.
//
// A single API header on purpose: modules call each other in both directions
// (net_paths <-> mqtt_io, sms_voice <-> modem_at), so per-module headers would
// have to include one another. Declaration order does not matter.
//
// Deliberately does NOT include cof_state.h: cof_state.h includes this file,
// and including back would close the guard before the types are in scope.
// Always include cof_state.h first.

// ---- owned by at_parse --------------------------------------
int atUrcCode(const String& resp, const char* tag);
bool ceerLooksNoAnswer(const String& ceer);
bool ceerLooksRejected(const String& ceer);
String compactAtText(const String& raw);
int compareVersions(const String& a, const String& b);
String extractAtTagValue(const String& response, const char* tag);
String extractQuoted(const String& response);
String firstNonEmptyAtLine(const String& response);
String lastQuoted(const String& text);
bool looksLikeIp(const String& ip);
String mqttTopic(const String& suffix);
String nthQuoted(const String& line, int want);
int parseCeerCode(const String& ceer);
int parseCommaStat(const String& response, const char* tag);
bool phoneLooksValid(const String& phone);
String withFirmware(const String& message);

// ---- owned by core ------------------------------------------
void handleButton();
void handleSerialCommand(const String& command);
void handleSerialInput();
void loop();
void maintainLteFallback();
bool networkStatRegistered(int stat);
int parseClccStat(const String& response);
void pollModem();
void printRuntimeStatus();
void printSerialHelp();
void publishTestCallProgress(const String& message);
void publishTestCallResult(const String& result, bool ok, const String& commandId = "");
String queryCallFailCause();
bool readTestButton();
void setStatus(const String& line);
void setup();

// ---- owned by lte_pdp ---------------------------------------
bool activateCnactPdp(String& ipOut);
bool activateNetopenPdp(String& ipOut);
void detectLteIpStack();
bool ensureLtePdp();
void finishLteAttempt(bool ok, const String& message);
bool markLtePdpUp(const String& ip, uint8_t cid);
bool netopenIsActive();
bool netopenResultOk(const String& resp);
bool parseLteIp(const String& resp, String& ipOut);
bool queryLteIp(String& ipOut);
// Logical UART mutex: take before voice/SMS AT, release after. Neither end
// disconnects CMQTT: the session lives in the module and survives the handover.
void takeModemForVoiceSms(ModemUartOwner owner);
void releaseModemToMqtt(bool wasOnLte);
bool modemUartOwnedByMqtt();
// General CS gate: no call/SMS until modem is past ATREADY/boot/LTE bring-up settle.
void noteModemUnstable(const char* reason);
bool modemCsWorkAllowed();
String resolveLteMqttPeer(const char* host);
void restorePacketServices();
void stopLtePdp();
// First cause wins; *ATREADY may append ("pub-dead+atready") until take.
void noteLteSessionDrop(const char* reason);
const char* takeLteSessionDrop();

// ---- owned by modem_at --------------------------------------
void appendModemLog(char direction, const String& text);
// Records a line even when no call/LTE handshake is in progress. Used so the
// device page shows CMQTT URCs and SMS AT that the gated logger drops.
void appendModemLogForced(const String& text);
// Persist + apply UART debug (NVS). Only the MQTT Flask command toggles it;
// neither boot nor OTA forces it ON.
void setModemUartDebug(bool enable, const char* reason);
// Queue a modem_uart_debug event with the current log (lab dumps).
void snapshotModemUartDebug(const char* reason);
// With debug ON: move live UART text into the outbound chunk queue (no wipe of
// meaning — sealed verbatim for later MQTT publish).
void sealModemUartDebugChunk(const char* reason);
void serviceModemUartDebug();
void captureLteUrcLog();
void beginInternalWatchdog();
void configureCellularApn();
bool cpinResponseReady(const String& response);
bool csAttached();
void feedWatchdog();
void flushModemInput();
bool initModem();
bool modemLineInteresting(const String& line);
bool modemWaitForPrompt(uint32_t timeoutMs);
void noteModemRebootDetected();
void noteSubscriberIdentity();
int queryCpas();
bool radioHasService();
bool radioIsGsm();
bool radioIsOnline();
bool radioReportsService();
String readModemUntil(uint32_t timeoutMs, const String& token = "", const String& errorToken = "");
void refreshCellularStatus();
void applyAdaptiveCemode();
void enableCsSmsTransport();
bool dropImsForSms();
void restoreImsMode();
void refreshRadioMode();
bool refreshSimReady();
bool resetModemRadio(uint8_t stage);
void restoreAutoRadio();
bool sendAT(const String& command, const String& expected = "OK", uint32_t timeoutMs = 2000, String* responseOut = nullptr);
// NUL-safe search for the reboot URC: the A7672 prefixes a spontaneous reset
// with `\0`, so String::indexOf("*ATREADY") (strstr) never sees it.
bool textHasAtReady(const String& text);
bool waitForRadioService(uint32_t timeoutMs, bool gsmOnly);
bool waitUntilModemReady(bool forCall, uint32_t timeoutMs);
void waitWithMqtt(uint32_t ms);
void waitWithWatchdog(uint32_t ms);

// ---- owned by lte_mqtt_native -------------------------------
bool cmqttConnect(const String& clientId, const String& willTopic, const String& willPayload,
                  const String& host, int port, const String& username, const String& password);
bool cmqttIsConnected();
bool cmqttIsRxBusy();
// CMQTTSTART is up (says nothing about the broker link). Used to tell a failed
// CONNECT over a dead bearer from a service that never started.
bool cmqttServiceIsUp();
void cmqttLoop();
bool cmqttPublish(const String& topic, const uint8_t* payload, size_t len, bool retained, uint8_t qos);
// Called when voice/SMS hands the UART back: keeps a session the module says is
// live, clears flags (no DISC/REL/STOP) when it says the session is gone.
void cmqttResumeAfterUartHandover();
bool cmqttSubscribe(const String& topic, uint8_t qos);
// Last resort only (LAN takes over for good, 3 failed CONNECTs, CSQ 99, radio
// ladder, credential wipe): DISC+REL+STOP, and DISC only if the module confirms
// a live session (DISC on a non-connected client answers +CMQTTDISC: 0,11 and
// chains REL/STOP into ERROR). Never call this from a hot path.
void cmqttTearDown();
void serviceLteMqttHealth();

// ---- owned by mqtt_io ---------------------------------------
void bounceMqttForRouteChange();
void configureMqttClientTransport();
void connectMqttIfNeeded();
void deferDeviceEvent(const char* type, const char* severity, const String& message,
                      const String& commandId, const String& transport = "");
void enforceMqttSilenceWatchdog();
void fillCellularJson(JsonObject cellular);
void fillConnectivityJson(JsonDocument& doc);
void fillNetworkJson(JsonObject network);
void flushDeferredEvents();
bool mqttUsesTls();
void onMqttMessage(char* topic, byte* payload, unsigned int length);
bool publishDeviceEvent(const char* type, const char* severity, const String& message,
                        const String& commandId = "", const String& transport = "");
void publishDeviceStatus(const char* status, bool retained = true);
void publishLteDataTrace();
bool publishMqttJson(const String& suffix, JsonDocument& doc, bool retained = false, uint8_t qos = 0);
bool publishTelemetryNow();
void requestMqttBounce(const char* reason);

// ---- owned by net_paths -------------------------------------
const char* activeNetworkName();
void applyPreferredRoute(PathPreference pref = PathPreference::Auto);
void beginEthernet();
void beginSavedWiFi();
bool canUseLan();
void clearSavedWiFi();
void connectWiFi(const String& ssid, const String& password, bool saveCredentials);
String currentIpAddress();
bool ethernetHoldoffActive();
void forgetWifiRadio();
bool lanConnected();
bool lanHasInternet();
bool lanPathReachable();
void maintainWifiBackup();
void markEthernetDown(const char* reason);
void markEthernetUp(const char* reason);
const char* mqttPathLetter();
bool networkConnected();
void noteLanMqttFailure(const char* reason);
void noteLanPathFailure(bool ethernet, const char* reason, bool hadInternet);
void onBrokerResolved(const char* name, const ip_addr_t* addr, void* arg);
void onNetworkEvent(WiFiEvent_t event, WiFiEventInfo_t info);
void pauseWiFiRadio();
void pollEthernetPath();
void pollWifiPath();
bool probeMqttOnInterface(bool ethernet);
bool probeMqttOverEthernet();
bool probeMqttOverWifi();
IPAddress resolveBrokerHost(const String& host, bool force);
void scheduleWifiBackup(uint32_t delayMs);
void serviceBrokerResolve();
void serviceNetworkPaths();
void startWifiRadio();

// ---- owned by ota_config ------------------------------------
bool applyDesiredConfig(JsonDocument& doc);
void checkManifest(bool allowFirmwareUpdate);
// Modem path of the pre-recorded audio for a text sha, or "" if not on device.
String ruleAudioPathForSha(const String& sha);
// ruleAudioPathForSha() plus an on-demand download of ``url`` when missing.
String ensureRuleAudio(const String& sha, const String& url);
void clearMqttConfig();
bool httpGetString(const String& url, String& out, uint32_t timeoutMs = 15000);
void initOtaRollbackGuard();
void loadSavedMqttConfig();
bool performOta(const String& url, const String& newVersion, const String& expectedSha256);
void publishCommandAck();
void publishConfigReported();
void saveMqttConfig(const String& host, int port, const String& deviceId, const String& username, const String& password);
void serviceOtaRollbackGuard();

// ---- owned by sensors_display -------------------------------
void detectPcf8574();
void drawDisplay();
String ds18b20AddressToString(const DeviceAddress address);
bool i2cDevicePresent(uint8_t address);
void initDisplay();
void readSensors();
void scanI2cBus();

// ---- owned by sms_voice -------------------------------------
void bounceRadioForCsfb();
bool callIsIdle();
String classifyCallUrc(const String& raw);
String classifyHangup(const String& ceer, bool sawAlerting, CallEndSource source);
String conductOutgoingCall(uint32_t timeoutMs, String* ceerOut);
String dialAndMaybePlay(const String& phone, const String& bearer);
bool imsVoiceReady();
String inferVoicePath();
bool isCallReady();
bool isSmsReady();
int lastClccStat(const String& response);
String observeVoicePath(const String& radioDial, const String& radioConnect);
int parseClccStatAt(const String& response, int tag);
void persistObservedVoicePath(const String& path);
void persistSkipGsm(bool skip);
String placeCallAndPlayAudio(const String& phoneOverride = "", bool adminTest = false, const String& audioSha = "", const String& audioUrl = "");
void pollIncomingSms();
String prepareVoiceBearer();
void processPendingSmsUrcs();
void publishCallModemSignal(const String& raw);
void publishInboundSms(const String& from, const String& text);
void publishSmsRecords(const String& response, const char* tag);
void runModemProbe(const String& commandId = "");
void runCmqttProbe(const String& commandId = "");
int queryClccStat();
String resolveTestPhone(const String& phoneOverride);
String sendTestSms(const String& phoneOverride, const String& text);
bool smsStackReady();
String stopPlaybackAndCollect();
String takePendingCallUrcs();
String transmitSms(const String& phone, const String& body, uint32_t timeoutMs = 60000);
String uploadAudioToModem(const String& url, const String& modemPath, const String& audioVersion);
bool fallbackAudioAvailable();
String voiceContextSuffix(const String& bearer, const String& ceer = "");
