nmarcovecchio/cof/firmware/src/lte_mqtt_client.h

#pragma once
// LteMqttClient: Client implementation that speaks MQTT over the modem's
// transparent-mode socket. Extracted verbatim from main.cpp.
//
// Its inline methods read the shared variables AND call the AT helpers, so it
// must be included after both. cof_state.h does that (variables, then
// cof_api.h, then this file), which is why the includes below find everything
// in scope.

#include <Arduino.h>
#include <Client.h>

#include "cof_config.h"
#include "cof_state.h"
#include "cof_api.h"

class LteMqttClient : public Client {
 public:
  uint8_t sock = 0;
  bool sockOpen = false;

  // Reentrancy guard for the UART's command mode.
  //
  // `write()` sends `AT+CIPSEND`, waits for the `>` prompt and then waits for
  // the `+CIPSEND:` ACK - three exchanges in which the module owns the line.
  // Both waits go through `readModemUntil()`, which pumps `mqttClient.loop()`,
  // and `loop()` calls `available()`, which on an empty RX buffer issues its own
  // `AT+CIPRXGET` (see `recvChunk()`). Injecting that command in the middle of
  // the send either swallows the `>` or steals the ACK, `modemWaitForPrompt()`
  // times out and the socket is torn down.
  //
  // Observed in the 2026-09-23 handshake: the MQTT CONNECT (sent while
  // `state.mqttConnected` was still false, so nothing pumped) completed with a
  // clean `+CIPSEND: 0,135,135` and a CONNACK, and the very next send - the
  // `subscribe`, issued after the flag was raised - died at "no '>' prompt".
  // The pump is what breaks the send, so it is the pump that has to stand down.
  bool atCommandBusy = false;
  uint8_t rxBuf[512];
  int rxLen = 0;
  int rxPos = 0;
  bool dataInd = false;

  void drainRx() {
    rxLen = 0;
    rxPos = 0;
    dataInd = false;
  }

  uint32_t lastRxPollMs = 0;

  // First window of the MQTT-over-LTE session, captured verbatim.
  //
  // The shared modem log (`modemCallLog`) is a ring that keeps only the TAIL, so
  // in a retry loop the first attempt - the only one whose send ACK, CONNACK and
  // PubSubClient state say *why* the connect failed - is always discarded. This
  // keeps the HEAD of the session instead, and is published next to the ring in
  // the `lte_data` event (see `publishLteDataTrace`, which clears it).
  //
  // Deliberately NOT reset per connect: the retry path tears the PDP down and
  // rebuilds it, so a per-open reset would keep erasing the attempt we want to
  // keep. It clears only once it has been published, so the failure that never
  // reaches a successful publish is exactly the one that survives.
  //
  // `LteMqttClient::write()` talks to ModemSerial directly instead of going
  // through `sendAT()`, which is why the MQTT handshake never reached the trace.
  String handshake;
  static constexpr size_t kHandshakeMax = 700;

  void noteHandshake(const String& entry) {
    if (handshake.length() >= kHandshakeMax) {
      return;
    }
    if (handshake.length() > 0) {
      handshake += '\n';
    }
    handshake += entry;
  }

  // Keep only printable ASCII so the handshake always serialises as valid JSON.
  // A module that reboots with echo ON returns control bytes (\x00, \x01) plus
  // its boot URCs; dumping those raw corrupted the event JSON (the worker wrapped
  // it in {"raw": ...} and the severity was lost). See BACKLOG §6h(b).
  String sanitizeHandshake(const String& raw) {
    String out;
    out.reserve(raw.length());
    for (unsigned i = 0; i < raw.length(); i++) {
      const char c = raw[i];
      if (c == '\n') {
        out += " | ";
      } else if (c == '\r') {
        // drop
      } else if (c >= 32 && c <= 126) {
        out += c;
      }
    }
    out.trim();
    if (out.length() > 160) {
      out = out.substring(0, 160);
    }
    return out;
  }

  bool useNetopen() const {
    return lteIpStack != kLteStackCnact;
  }

  void noteUrc(const String& line) {
    if (line.startsWith("+CADATAIND:") || line.startsWith("+CARECV:") ||
        line.startsWith("+CIPRXGET: 1")) {
      dataInd = true;
    } else if (line.startsWith("+CIPEVENT:")) {
      // +CIPEVENT: NETWORK CLOSED UNEXPECTEDLY = the network library died (out
      // of service). That is a dead PDP, not just a closed socket: flag a PDP
      // rebuild so connectMqttIfNeeded() tears it down instead of dialing a
      // dead context. Any other +CIPEVENT is treated as a passive close.
      sockOpen = false;
      if (line.indexOf("NETWORK CLOSED") >= 0) {
        ltePdpDown = true;
      }
    } else if (line.startsWith("+IPCLOSE:") ||
               (line.startsWith("+CASTATE:") && line.indexOf(",0") > 0)) {
      // Socket closed passively (remote close / send timeout). The PDP is still
      // alive: the next connect just reopens the socket (CIPOPEN). Tearing the
      // PDP down here turned a ~5 s broker close into a ~45 s NETCLOSE/NETOPEN
      // rebuild and a visible MQTT "cut".
      sockOpen = false;
    }
    // The A7672 emits *ATREADY only on module (re)boot. A spontaneous reset or
    // the recovery ladder's CFUN=1,1 both produce it, and it leaves the AT
    // channel in echo mode with the APN config lost. Just record it here; the
    // reset itself happens in pollModem() (outside any in-flight command), see
    // noteModemRebootDetected().
    if (line.indexOf("*ATREADY") >= 0) {
      modemRebootUrcSeen = true;
    }
  }

  void pumpUrcs() {
    // Bound the number of lines drained per call: with a module spewing URCs the
    // outer loop used to run forever inside available() and starve the MQTT pump.
    int lines = 0;
    while (ModemSerial.available() && lines < 16) {
      String line;
      const uint32_t start = millis();
      while (millis() - start < 50) {
        if (!ModemSerial.available()) {
          delay(1);
          continue;
        }
        const char c = static_cast<char>(ModemSerial.read());
        if (c == '\n') {
          break;
        }
        if (c != '\r') {
          line += c;
        }
      }
      lines++;
      line.trim();
      if (line.length() == 0) {
        continue;
      }
      noteUrc(line);
      if (!line.startsWith("+CIPRXGET: 1") && !line.startsWith("+CADATAIND:") &&
          !line.startsWith("+CARECV:")) {
        pendingModemUrcs += line + "\n";
      }
    }
    if (pendingModemUrcs.indexOf("+CIPRXGET: 1") >= 0 ||
        pendingModemUrcs.indexOf("+CADATAIND:") >= 0) {
      dataInd = true;
    }
    if (pendingModemUrcs.indexOf("+IPCLOSE:") >= 0 ||
        pendingModemUrcs.indexOf("+CIPEVENT:") >= 0) {
      sockOpen = false;
    }
  }

  bool recvChunk() {
    if (rxPos < rxLen) {
      return true;
    }
    rxLen = 0;
    rxPos = 0;
    const bool netopen = useNetopen();
    if (netopen) {
      ModemSerial.print("AT+CIPRXGET=2,");
      ModemSerial.print(sock);
      ModemSerial.print(",512\r\n");
    } else {
      ModemSerial.print("AT+CARECV=");
      ModemSerial.print(sock);
      ModemSerial.print(",512\r\n");
    }
    String header;
    const uint32_t startedAt = millis();
    const char* tag = netopen ? "+CIPRXGET: 2," : "+CARECV:";
    while (millis() - startedAt < 3000) {
      feedWatchdog();
      // Bound the drain and the header buffer: an echo'd command plus a boot-URC
      // flood used to grow `header` without limit and keep this loop spinning
      // until it exhausted the heap (see readModemUntil's matching guard).
      while (ModemSerial.available() && header.length() < 1024) {
        const char c = static_cast<char>(ModemSerial.read());
        header += c;
        const int tagAt = header.indexOf(tag);
        const int nl = tagAt >= 0 ? header.indexOf('\n', tagAt) : -1;
        if (tagAt >= 0 && nl > tagAt) {
          const String line = header.substring(tagAt, nl);
          int n = 0;
          if (netopen) {
            const int c1 = line.indexOf(',');
            const int c2 = c1 >= 0 ? line.indexOf(',', c1 + 1) : -1;
            const int c3 = c2 >= 0 ? line.indexOf(',', c2 + 1) : -1;
            if (c2 >= 0 && c3 > c2) {
              n = line.substring(c2 + 1, c3).toInt();
            } else if (c2 >= 0) {
              n = line.substring(c2 + 1).toInt();
            }
          } else {
            const int comma = line.indexOf(',');
            if (comma >= 0) {
              n = line.substring(comma + 1).toInt();
            }
          }
          if (n <= 0) {
            dataInd = false;
            return false;
          }
          if (n > static_cast<int>(sizeof(rxBuf))) {
            n = sizeof(rxBuf);
          }
          int got = 0;
          while (got < n && millis() - startedAt < 3000) {
            feedWatchdog();
            if (ModemSerial.available()) {
              rxBuf[got++] = static_cast<uint8_t>(ModemSerial.read());
            }
          }
          rxLen = got;
          rxPos = 0;
          dataInd = false;
          return rxLen > 0;
        }
        if (header.indexOf("ERROR") >= 0) {
          dataInd = false;
          return false;
        }
      }
      delay(5);
    }
    dataInd = false;
    return false;
  }

  int connect(IPAddress ip, uint16_t port) override {
    return connect(ip.toString().c_str(), port);
  }

  int connect(const char* host, uint16_t port) override {
    stop();
    if (!state.lteDataUp) {
      return 0;
    }
    noteHandshake(String("open ") + host + ":" + String(port) +
                  (useNetopen() ? " netopen" : " cnact"));
    String resp;
    if (useNetopen()) {
      sendAT(String("AT+CIPCLOSE=") + String(sock), "OK", 5000);
      sendAT("AT+CIPRXGET=1", "OK", 3000);
      const String peer = resolveLteMqttPeer(host);
      String cmd = String("AT+CIPOPEN=") + String(sock) + ",\"TCP\",\"" + peer + "\"," + String(port);
      if (!sendAT(cmd, "+CIPOPEN:", 25000, &resp)) {
        Serial.println("[lte] CIPOPEN fail");
        noteHandshake("CIPOPEN no response: " + sanitizeHandshake(resp));
        sockOpen = false;
        return 0;
      }
      const int err = atUrcCode(resp, "+CIPOPEN:");
      if (err != 0) {
        Serial.printf("[lte] CIPOPEN err %d %s\n", err, resp.c_str());
        noteHandshake(String("CIPOPEN err ") + String(err) + ": " + sanitizeHandshake(resp));
        sendAT(String("AT+CIPCLOSE=") + String(sock), "OK", 5000);
        sockOpen = false;
        return 0;
      }
      Serial.printf("[lte] TCP %s:%u via %s NETOPEN\n", host, port, peer.c_str());
      noteHandshake("CIPOPEN ok " + peer);
    } else {
      const char* proto = mqttUsesTls() ? "SSL" : "TCP";
      if (mqttUsesTls()) {
        sendAT("AT+CASSLCFG=0,\"ssl\",1", "OK", 3000);
      }
      String cmd = String("AT+CAOPEN=0,") + String(sock) + ",\"" + proto + "\",\"" + host + "\"," +
                   String(port);
      if (!sendAT(cmd, "+CAOPEN:", 25000, &resp) || atUrcCode(resp, "+CAOPEN:") != 0) {
        Serial.printf("[lte] CAOPEN err %s\n", resp.c_str());
        sockOpen = false;
        return 0;
      }
      Serial.printf("[lte] TCP %s:%u %s CNACT\n", host, port, proto);
    }
    drainRx();
    sockOpen = true;
    lastRxPollMs = millis();
    return 1;
  }

  size_t write(uint8_t b) override {
    return write(&b, 1);
  }

  size_t write(const uint8_t* buf, size_t size) override {
    if (!sockOpen || buf == nullptr || size == 0) {
      return 0;
    }
    size_t sent = 0;
    while (sent < size) {
      size_t chunk = size - sent;
      if (chunk > 1024) {
        chunk = 1024;
      }
      // Own the line for the whole send: prompt, payload and ACK. `available()`
      // must not emit AT until this drops or it corrupts the exchange.
      atCommandBusy = true;
      if (useNetopen()) {
        ModemSerial.print("AT+CIPSEND=");
      } else {
        ModemSerial.print("AT+CASEND=");
      }
      ModemSerial.print(sock);
      ModemSerial.print(",");
      ModemSerial.print(static_cast<unsigned>(chunk));
      ModemSerial.print("\r\n");
      if (!modemWaitForPrompt(5000)) {
        atCommandBusy = false;
        noteHandshake("no '>' prompt for CIPSEND");
        sockOpen = false;
        return sent;
      }
      ModemSerial.write(buf + sent, chunk);
      const String token = useNetopen() ? "+CIPSEND:" : "OK";
      const String resp = readModemUntil(15000, token);
      atCommandBusy = false;
      // Capture the send verdict: this is the step the old trace could never
      // show, because write() is the one AT path that does not go through
      // sendAT(). Keep ONLY the ACK shape - never the echoed command or the
      // payload. When the module reboots with echo ON the raw response carries
      // the binary MQTT bytes (client id, will, username and the plaintext
      // password), which must not reach the handshake (see BACKLOG §6h(b)).
      {
        String verdict;
        if (resp.indexOf("ERROR") >= 0) {
          verdict = "ERROR";
        } else {
          const String ackTag = useNetopen() ? "+CIPSEND:" : "OK";
          const int ackAt = resp.indexOf(ackTag);
          if (ackAt < 0) {
            verdict = "(no ACK)";
          } else {
            int ackEnd = resp.indexOf('\n', ackAt);
            if (ackEnd < 0) {
              ackEnd = resp.indexOf('\r', ackAt);
            }
            if (ackEnd < 0) {
              ackEnd = resp.length();
            }
            verdict = resp.substring(ackAt, ackEnd);
            verdict.replace("\r", " ");
            verdict.trim();
          }
        }
        noteHandshake(String("CIPSEND ") + String(chunk) + " -> " + verdict);
      }
      if (resp.indexOf("ERROR") >= 0 || (useNetopen() && resp.indexOf("+CIPSEND:") < 0) ||
          (!useNetopen() && resp.indexOf("OK") < 0)) {
        sockOpen = false;
        return sent;
      }
      sent += chunk;
    }
    return sent;
  }

  int available() override {
    if (!sockOpen) {
      return 0;
    }
    if (rxPos < rxLen) {
      return rxLen - rxPos;
    }
    // A `write()` in flight owns the UART until its ACK lands. Issuing
    // `AT+CIPRXGET` here would land inside the `AT+CIPSEND` exchange and break
    // it (see `atCommandBusy`). Report "nothing buffered" instead so
    // PubSubClient's pump keeps running without touching the module.
    if (atCommandBusy) {
      return 0;
    }
    pumpUrcs();
    if (!dataInd && useNetopen() && millis() - lastRxPollMs >= 250) {
      lastRxPollMs = millis();
      dataInd = true;
    }
    if (dataInd) {
      recvChunk();
    }
    return rxLen - rxPos;
  }

  int read() override {
    if (available() <= 0) {
      return -1;
    }
    return rxBuf[rxPos++];
  }

  int read(uint8_t* buf, size_t size) override {
    if (buf == nullptr || size == 0) {
      return 0;
    }
    int n = 0;
    while (n < static_cast<int>(size) && available() > 0) {
      buf[n++] = rxBuf[rxPos++];
    }
    return n;
  }

  int peek() override {
    if (available() <= 0) {
      return -1;
    }
    return rxBuf[rxPos];
  }

  void flush() override {}

  void stop() override {
    if (sockOpen) {
      if (useNetopen()) {
        sendAT(String("AT+CIPCLOSE=") + String(sock), "OK", 8000);
      } else {
        sendAT(String("AT+CACLOSE=") + String(sock), "OK", 5000);
      }
    }
    sockOpen = false;
    // A write() interrupted mid-exchange leaves this set; a stuck guard would
    // silently disable all inbound reads for the next session.
    atCommandBusy = false;
    drainRx();
  }

  uint8_t connected() override {
    return sockOpen ? 1 : 0;
  }

  operator bool() {
    return connected();
  }
};
